keyandcableco/8bit8asterd/generate.py

#!/usr/bin/env python3
# 8-Bit 8asterd -- parameter bank generator.
#
# Copyright (C) 2026 Greg Miller, The Key & Cable Company
#
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
"""
8b8 parameter bank generator
============================

Single source of truth for the 8-Bit 8asterd's controllable parameters.
Edit PARAMS / PRESETS below, run this script, and it regenerates:

  parameters.h   -> include from the firmware (.ino). Param indices, ranges,
                    defaults, and a layout-version byte used to invalidate
                    stale EEPROM saves whenever the definition changes.
  index.html     -> the Web Serial control panel (Chrome/Edge, open the file
                    directly). All controls, groupings, display scaling and
                    factory presets are generated from PARAMS/PRESETS.

Protocol (USB-CDC serial, 115200, newline-terminated ASCII):
  P:<idx>:<value>   set one parameter        -> reply  V:<idx>:<clamped>
  DUMP              request all values       -> reply  PRESET:<v0>,<v1>,...
  LOAD:<v0>,<v1>,.. apply a full preset      -> reply  PRESET:...
  SAVE              persist params to EEPROM -> reply  SAVED:1
  DEFAULTS          restore factory defaults -> reply  PRESET:...

A preset is nothing more than the PRESET: CSV — an array of values in
parameter-index order, same idea as the minichord's parameter banks.
"""

import json
import os
import sys

from temperaments import PROFILES as TEMPER_PROFILES

# Panel labels per temperament, in profile order. Enum buttons are narrow, so
# a few are abbreviated; the full names stay in temperaments.py. Any profile
# without an entry here shows its own label, so a new one appears unnamed
# rather than not at all.
TEMPER_SHORT = {"quarter-comma meantone": "Meantone", "five-limit just (C major)": "Just",
                "pythagorean": "Pythag", "werckmeister III": "Werck III",
                "kirnberger III": "Kirn III", "vallotti": "Vallotti",
                "young no. 2": "Young", "kellner": "Kellner",
                "sixth-comma meantone": "1/6 Mean", "equal": "Equal"}
TEMPER_LABELS = [TEMPER_SHORT.get(p["name"], p["label"]) for p in TEMPER_PROFILES]

# ---------------------------------------------------------------------------
# Parameter definitions
# ---------------------------------------------------------------------------
# kind:    "toggle" (0/1 switch), "int" (slider), "enum" (button row; the
#          stored value is the option INDEX — firmware maps it to hardware
#          values where needed, e.g. buzz shape index -> AY shape register)
# scale/unit/offset: display only. shown = (value + offset) * scale
# help:    one line shown under the control
#
# All values must fit in a uint8_t (0..255) — the firmware stores the bank
# as a flat uint8_t array and EEPROM-persists it byte-for-byte.

PARAMS = [
    # --- Buzzy Bass --------------------------------------------------------
    dict(key="buzz_enable", label="Enable", group="Buzzy Bass", kind="toggle",
         default=0,
         help="Points the lowest held note's volume at the chip's envelope generator. Set to a looping shape it is an oscillator, so the note becomes a sawtooth or triangle rather than a square."),
    dict(key="buzz_ratio", label="Ratio", group="Buzzy Bass", kind="int",
         min=1, max=8, default=1,
         help="How far below the note the envelope oscillates: 1 is unison, 2 an octave down, 4 two octaves. At unison it is a waveform; lower it becomes a sub-oscillator."),
    dict(key="buzz_shape", label="Shape", group="Buzzy Bass", kind="enum",
         options=["Saw \u2193", "Tri \u2193\u2191", "Saw \u2191", "Tri \u2191\u2193"],
         default=0,
         help="Which looping envelope shape the hardware runs: 0 and 2 are sawtooths, 1 and 3 triangles. This is where a non-square waveform comes from -- the chip has no other."),
    dict(key="buzz_pure", label="Pure", group="Buzzy Bass", kind="toggle",
         default=0,
         help="Closes the channel's tone gate, so only the envelope reaches "
              "the output. Off, the square still gates the envelope and you "
              "hear the product of the two; on, you get the hardware "
              "sawtooth or triangle by itself."),
    dict(key="buzz_detune", label="Detune", group="Buzzy Bass", kind="int",
         min=0, max=64, default=32, offset=-32,
         help="Offsets the envelope against the square wave. Non-zero gives "
              "the sweeping 'MadMax buzzer' beat. 0 = locked together."),

    # --- Warp Zone (digital circuit bending) -------------------------------
    # Software versions of what a hardware bend does: hit the chip with
    # writes it was never meant to get, fast, while notes are sounding.
    # These write STRAIGHT to the chip, bypassing the register cache, so the
    # normal voice updates keep fighting them -- that fight is the sound.
    dict(key="warp_mode", label="Mode", group="Warp Zone", kind="enum",
         options=["Off", "Sync Buzz", "Stutter", "Scramble", "Zap",
                  "Tape Stop", "Siren", "Crush", "Ring", "Env Crush",
                  "SID Voice"],
         default=0,
         help="Sync Buzz restarts the envelope. Stutter gates the mixer. "
              "Scramble throws junk at registers. Zap sweeps noise. The "
              "last four move on their own: Tape Stop drags pitch down and "
              "snaps back, Siren sweeps it, Crush quantises it coarser and "
              "coarser, Ring is audio-rate amplitude modulation."),
    dict(key="warp_rate", label="Rate", group="Warp Zone", kind="int",
         min=1, max=120, default=30,
         help="Low = slow chopping. High reaches audio rate and becomes a "
              "tone in its own right. In Clock Warp, 1 holds the clock down "
              "instead of sweeping it, the way a clock-halving switch does."),
    dict(key="warp_depth", label="Depth", group="Warp Zone", kind="int",
         min=1, max=63, default=20,
         help="How violent the effect is."),
    dict(key="clock_enable", label="Enable", group="Clock Warp", kind="toggle",
         default=0,
         help="Wobbles the AY master clock, which the Leonardo generates, so "
              "it sits upstream of all three chips: pitch, noise colour, "
              "envelope rates and drum decays move together. It touches no "
              "chip register, so it runs alongside any Warp Zone mode."),
    dict(key="clock_drop", label="Drop", group="Clock Warp", kind="int",
         min=0, max=63, default=30,
         help="How far the clock falls. Around 45 matches the halving a "
              "YM2149 gives with its SEL pin low; full reaches 380kHz, below "
              "anything a hardware switch does."),
    dict(key="clock_sweep", label="Sweep", group="Clock Warp", kind="int",
         min=1, max=120, default=20,
         help="How fast the clock wanders. Only audible while Hold is below "
              "maximum, since a held clock does not sweep."),
    dict(key="clock_hold", label="Hold", group="Clock Warp", kind="int",
         min=0, max=63, default=0,
         help="Mixes between sweeping and sitting at the bottom of the "
              "sweep. Full is a clock-halving switch held down, which is "
              "where the coarse, slow character lives."),

    dict(key="warp_motion", label="Motion", group="Warp Zone", kind="int",
         min=0, max=64, default=0,
         help="Sweeps Rate up and down on its own, hands free. The sweep "
              "itself is usually the interesting part, not where it "
              "settles. 0 = Rate stays put."),

    # --- Vibrato -----------------------------------------------------------
    dict(key="wave_enable", label="Enable", group="Wavetable", kind="toggle",
         default=0,
         help="Takes over one channel and writes its volume register from a "
              "table at audio rate, tone off. The register becomes a 4-bit "
              "DAC, so the voice plays a real waveform instead of a square. "
              "Costs a voice and follows the highest note held."),
    dict(key="wave_shape", label="Shape", group="Wavetable", kind="enum",
         options=["Sine", "Triangle", "Saw", "Ramp", "Pulse 25%", "Vocal"],
         default=0,
         help="Sine and triangle are softer than anything the chip makes on "
              "its own. Pulse gives the narrow-square sound the AY cannot do "
              "in hardware. Vocal is a formant shape, somewhere near an 'ah'."),
    dict(key="wave_level", label="Level", group="Wavetable", kind="int",
         min=1, max=15, default=12,
         help="Peak of the waveform. Low values lose resolution fast, since "
              "there are only sixteen amplitude steps to draw it with."),

    dict(key="draw_enable", label="Enable", group="Drawbars", kind="toggle",
         default=0,
         help="Adds harmonics of each note on further voices, the way an "
              "organ's drawbars do. Summed squares at these ratios reshape "
              "the timbre rather than just thickening it, which is the only "
              "route to a new tone colour on a chip with no filter. Costs a "
              "voice per stop, so polyphony falls accordingly."),
    dict(key="draw_a", label="Stop 1", group="Drawbars", kind="enum",
         options=["Off", "16'", "5 1/3'", "4'", "2 2/3'", "2'", "1 3/5'", "1 1/3'", "1'"],
         default=3,
         help="Pitch of the first added stop, in organ footages against the "
              "note at 8'. 16' is an octave below, 4' an octave above, "
              "2 2/3' a twelfth above."),
    dict(key="draw_a_level", label="Level 1", group="Drawbars", kind="int",
         min=1, max=15, default=8,
         help="How loud the first stop sits under the note."),
    dict(key="draw_b", label="Stop 2", group="Drawbars", kind="enum",
         options=["Off", "16'", "5 1/3'", "4'", "2 2/3'", "2'", "1 3/5'", "1 1/3'", "1'"],
         default=0,
         help="Pitch of the second added stop. Off leaves the voice free for "
              "polyphony."),
    dict(key="draw_b_level", label="Level 2", group="Drawbars", kind="int",
         min=1, max=15, default=6,
         help="How loud the second stop sits under the note."),

    dict(key="uni_enable", label="Enable", group="Unison", kind="toggle",
         default=0,
         help="Doubles each melodic note on a second voice a little out of "
              "tune with the first. Halves how many notes can sound at once, "
              "and the beating between the pair is what makes it wide."),
    dict(key="uni_detune", label="Detune", group="Unison", kind="int",
         min=1, max=32, default=8,
         help="How far apart the pair sits. Low values beat slowly and "
              "thicken; high values drift towards a chorus or an out-of-tune "
              "honky-tonk."),

    dict(key="vib_enable", label="Enable", group="Vibrato", kind="toggle",
         default=0,
         help="Pitch LFO on all sounding melodic voices. Drums untouched."),
    dict(key="vib_rate", label="Rate", group="Vibrato", kind="int",
         min=1, max=200, default=50, scale=0.1, unit="Hz",
         help=""),
    dict(key="vib_depth", label="Depth", group="Vibrato", kind="int",
         min=0, max=31, default=6,
         help=""),
    dict(key="vib_delay", label="Delay", group="Vibrato", kind="int",
         min=0, max=200, default=0, scale=10, unit="ms",
         help="Onset delay after note start, then fades in."),

    # --- Tremolo -----------------------------------------------------------
    dict(key="trem_enable", label="Enable", group="Tremolo", kind="toggle",
         default=0,
         help="Volume LFO on melodic voices."),
    dict(key="trem_rate", label="Rate", group="Tremolo", kind="int",
         min=1, max=200, default=40, scale=0.1, unit="Hz",
         help=""),
    dict(key="trem_depth", label="Depth", group="Tremolo", kind="int",
         min=0, max=15, default=5,
         help="How many volume steps the LFO cuts (AY volume is 0\u201315)."),

    # --- Noise Blend -------------------------------------------------------
    dict(key="noise_enable", label="Enable", group="Noise Blend", kind="toggle",
         default=0,
         help="Mixes the AY noise generator into melodic voices."),
    dict(key="noise_period", label="Period", group="Noise Blend", kind="int",
         min=0, max=15, default=8,
         help="Higher = darker noise. Per-chip register, shared with drums."),

    # --- Drums (global shaping of the CH10 kit) ----------------------------
    # These scale the built-in kit table in the firmware rather than
    # replacing it, so one set of controls reshapes every drum at once and
    # still fits the flat preset array.
    dict(key="drum_tune", label="Tune", group="Drums", kind="int",
         min=50, max=200, default=100, unit="%",
         help="Pitch of every tuned drum. 100 = the kit as built."),
    dict(key="drum_decay", label="Decay", group="Drums", kind="int",
         min=50, max=200, default=100, unit="%",
         help="Length of every drum. Higher = longer tails."),
    dict(key="drum_bend", label="Bend", group="Drums", kind="int",
         min=0, max=200, default=100, unit="%",
         help="Pitch-drop amount on kicks and toms. 0 = flat, no sweep."),
    dict(key="drum_noise", label="Noise", group="Drums", kind="int",
         min=0, max=14, default=7, offset=-7,
         help="Noise colour. Negative = brighter/hissier, positive = darker."),

    # --- Drum FX -----------------------------------------------------------
    # Drums are the only voices driven by the AY envelope generator, so
    # these reach things the tone effects cannot: restarting the envelope
    # mid-hit, running it backwards, and varying it per strike.
    dict(key="drum_roll", label="Roll", group="Drum FX", kind="int",
         min=0, max=50, default=0, unit="Hz",
         help="Re-strikes the envelope while a drum is still ringing. Low "
              "values flam, high values become a buzz roll. The fader is "
              "spaced by ratio rather than by Hz, so it moves evenly by ear "
              "all the way up. 0 = off."),
    dict(key="drum_flam", label="Flam", group="Drum FX", kind="int",
         min=0, max=30, default=0, scale=10, unit="ms",
         help="Every hit fires a second time this long after. 0 = off."),
    dict(key="drum_reverse", label="Reverse", group="Drum FX", kind="toggle",
         default=0,
         help="Runs the envelope upward so drums swell instead of decay, "
              "then cut. Reverse-cymbal territory."),
    dict(key="drum_chaos", label="Chaos", group="Drum FX", kind="int",
         min=0, max=63, default=0,
         help="Randomises pitch, noise colour and length on every single "
              "hit, so no two strikes are identical."),

    # --- Auto FX (NES tracker style, automatic per note) -------------------
    # The 2A03's sweep unit did pitch slides in hardware; its chord and
    # retrigger sounds came from the tracker re-writing registers every
    # frame. Both are software here, applied automatically on every note.
    dict(key="arp_mode", label="Arp", group="Auto FX", kind="enum",
         options=["Off", "Maj", "Min", "Oct", "5th", "Dim", "Wide"],
         default=0,
         help="Cycles one voice through a chord fast enough to hear it as a "
              "chord. The classic chiptune fake-polyphony trick."),
    dict(key="arp_rate", label="Arp Rate", group="Auto FX", kind="int",
         min=1, max=50, default=17, unit="Hz",
         help="Steps per second. Around 15-25 is the classic NES rattle."),
    dict(key="sweep_amount", label="Sweep", group="Auto FX", kind="int",
         min=0, max=64, default=32, offset=-32,
         help="Automatic pitch slide on every note, like the NES sweep "
              "unit. Negative falls, positive rises, 0 is off."),
    dict(key="retrig_rate", label="Retrigger", group="Auto FX", kind="int",
         min=0, max=50, default=0, unit="Hz",
         help="Re-strikes the envelope while a note is held. Spaced by "
              "ratio rather than by Hz, so it moves evenly by ear. 0 = off."),

    # --- Envelope ----------------------------------------------------------
    dict(key="env_mode", label="Mode", group="Envelope", kind="enum",
         options=["MIDI ch presets", "Custom ADSR"], default=0,
         help="Presets = the original per-MIDI-channel tones[] table."),
    dict(key="env_attack", label="Attack", group="Envelope", kind="int",
         min=1, max=32, default=1,
         help="How long the note takes to reach full level, from 10ms at 1 up to 4s at 32. Spaced by ratio, so the fader moves evenly by ear."),
    dict(key="env_decay", label="Decay", group="Envelope", kind="int",
         min=1, max=32, default=26,
         help="How long it takes to fall from full level to the Sustain "
              "level. Spaced by ratio, so the fader moves evenly by ear."),
    dict(key="env_sustain", label="Sustain", group="Envelope", kind="int",
         min=0, max=32, default=32,
         help=""),
    dict(key="env_release", label="Release", group="Envelope", kind="int",
         min=1, max=32, default=19,
         help="How long the note takes to fade once you let go."),

    # --- Pitch & Response --------------------------------------------------
    dict(key="glide", label="Glide", group="Pitch & Response", kind="int",
         min=0, max=100, default=0,
         help="Portamento from the previous note. 0 = off, higher = slower."),
    dict(key="transpose", label="Transpose", group="Pitch & Response", kind="int",
         min=0, max=48, default=24, offset=-24, unit="st",
         help=""),
    # --- Master Mixer ------------------------------------------------------
    dict(key="mix_noise", label="Noise", group="Mixer", kind="int",
         min=0, max=15, default=15,
         help="Master noise level. The chip has no noise fader -- tone and "
              "noise share one amplitude -- so this gates the noise on and "
              "off a few thousand times a second with a random duty. Random "
              "rather than regular keeps the artefact broadband, so it reads "
              "as quieter noise instead of a whine. 15 = untouched."),
    dict(key="mix_tone", label="Tone", group="Mixer", kind="int",
         min=0, max=15, default=15,
         help="Master level for the pitched voices. Drums are unaffected."),
    dict(key="mix_drum", label="Drums", group="Mixer", kind="int",
         min=0, max=15, default=15,
         help="Master drum level. Below 15 this moves drums off the chip's "
              "hardware envelope onto a software one so the level can be "
              "scaled at all, which softens the transient slightly. "
              "15 leaves them on the hardware envelope, untouched."),

    dict(key="temperament", label="Temperament", group="Tuning", kind="enum",
         # Derived from temperaments.py rather than typed out, so a
         # temperament added there reaches the parameter's range. A hand copy
         # stopped at ten and the firmware clamped anything past it away.
         options=[TEMPER_LABELS[i] for i in range(len(TEMPER_LABELS))],
         default=0,
         help="Historical tunings, and two divisions of the octave. Audible in "
              "the lower octaves; above about MIDI 72 the AY's integer divisor "
              "is too coarse to render the offsets and they round away. 19-EDO "
              "and 31-EDO put twelve of their notes on the keys in the meantone "
              "layout; Root moves that layout with the key."),
    dict(key="temper_root", label="Root", group="Tuning", kind="enum",
         options=["C", "C#", "D", "D#", "E", "F", "F#", "G", "G#", "A", "A#", "B"],
         default=0,
         help="Which key the temperament is centred on. The root itself is "
              "exactly in tune; everything else is tempered around it."),

    dict(key="vel_sense", label="Velocity", group="Pitch & Response", kind="toggle",
         default=1,
         help="Off = every note plays at full volume."),
]

# Factory presets, defined by key so they survive reordering of PARAMS.
# Missing keys fall back to the parameter's default.
# Patches kept out of the normal list because they sit at the far end of
# several controls at once. Not unstable in the sense of crashing -- the
# clamps still hold -- but loud, detuned and hard to play.
HIDDEN_PRESETS = {
    "Dead Air":     dict(clock_enable=1, clock_drop=63, clock_hold=63,
                         warp_mode=7, warp_rate=90, warp_depth=55),
    "Wasp Factory": dict(warp_mode=10, warp_rate=120, warp_depth=63,
                         wave_enable=1, wave_shape=4, wave_level=15),
    "Cathedral":    dict(draw_enable=1, draw_a=1, draw_a_level=15,
                         draw_b=4, draw_b_level=12,
                         buzz_enable=1, buzz_pure=1, buzz_ratio=2),
    "Wrong Speed":  dict(clock_enable=1, clock_drop=50, clock_hold=20,
                         clock_sweep=3, uni_enable=1, uni_detune=26),
    "Hornet":       dict(warp_mode=10, warp_rate=120, warp_depth=63,
                         buzz_enable=1, buzz_ratio=1, buzz_detune=6,
                         draw_enable=1, draw_a=8, draw_a_level=9),
}

PRESETS = {
    "Init": {},
    "Buzz Bass Lead": dict(buzz_enable=1, buzz_ratio=1, buzz_shape=0,
                           vib_enable=1, vib_rate=55, vib_depth=5, vib_delay=60),
    "Haunted Organ": dict(vib_enable=1, vib_rate=30, vib_depth=12,
                          trem_enable=1, trem_rate=35, trem_depth=6,
                          env_mode=1, env_attack=22, env_decay=30,
                          env_sustain=28, env_release=21),
    "Wind Machine": dict(noise_enable=1, noise_period=13,
                         trem_enable=1, trem_rate=25, trem_depth=7,
                         env_mode=1, env_attack=20, env_decay=32,
                         env_sustain=30, env_release=30, vel_sense=0),
    "Chip Whistle": dict(transpose=36, glide=25,
                         vib_enable=1, vib_rate=80, vib_depth=4, vib_delay=40),
    "808 Kit": dict(drum_tune=78, drum_decay=165, drum_bend=130, drum_noise=9),
    "Tight Kit": dict(drum_tune=118, drum_decay=62, drum_bend=70, drum_noise=5),
    "MadMax Buzzer": dict(buzz_enable=1, buzz_ratio=1, buzz_shape=1,
                          buzz_detune=38, env_mode=1, env_attack=1,
                          env_decay=31, env_sustain=30, env_release=24),
    "Arcade Warp": dict(warp_mode=1, warp_rate=95, warp_depth=40,
                        buzz_enable=1, buzz_ratio=2, buzz_detune=36),
    "Broken Cabinet": dict(warp_mode=3, warp_rate=22, warp_depth=55,
                           noise_enable=1, noise_period=6),
    "Tape Eaten": dict(warp_mode=5, warp_rate=70, warp_depth=34,
                       warp_motion=12),
    "Air Raid": dict(warp_mode=6, warp_rate=60, warp_depth=44,
                     warp_motion=20),
    "Dying Console": dict(warp_mode=7, warp_rate=48, warp_depth=40,
                          warp_motion=9, noise_enable=1, noise_period=9),
    "Ring Zone": dict(warp_mode=8, warp_rate=105, warp_depth=30,
                      warp_motion=26, buzz_enable=1, buzz_ratio=1),
    "Buzz Roll": dict(drum_roll=45, drum_decay=70, drum_chaos=10),
    "Drunk Drummer": dict(drum_flam=7, drum_chaos=38, drum_tune=92,
                          drum_decay=120),
    "Reverse Kit": dict(drum_reverse=1, drum_decay=150, drum_bend=40),
    "Broken Machine": dict(drum_roll=50, drum_chaos=58, drum_noise=4,
                           drum_decay=55, drum_bend=170),
    "Bad Ground": dict(warp_mode=3, warp_rate=6, warp_depth=38,
                       warp_motion=35, noise_period=6),
    "1-Up Arp": dict(arp_mode=1, arp_rate=20, env_mode=1, env_attack=1,
                     env_decay=28, env_sustain=26, env_release=26),
    "Laser Jump": dict(sweep_amount=52, env_mode=1, env_attack=1,
                       env_decay=25, env_sustain=6, env_release=30),
    "Machine Gun": dict(retrig_rate=38, noise_enable=1, noise_period=4,
                        env_mode=1, env_attack=1, env_decay=23,
                        env_sustain=10, env_release=28),
}

# ---------------------------------------------------------------------------
# Panel sections
# ---------------------------------------------------------------------------
# Tones and drums are different voices sharing the same three chips, and the
# FX reach across both. The panel says so out loud rather than leaving it to
# be discovered: each band is labelled with what it touches, and the Warp
# Zone sits across the bottom spanning both because it hits them differently.

# Where the published site lives. The social preview needs ABSOLUTE urls --
# Reddit, Discord and the rest will not resolve a relative one.
SITE_URL = "https://keyandcableco.github.io/8bit8asterd"
SITE_HOME = "https://keyandcable.com"
SITE_TITLE = "The 8Bit 8asterd"
SITE_DESC = ("A 9-voice chiptune synth built on three AY-3-8910 chips. "
             "Playable in your browser, running the same firmware as the hardware.")

SECTIONS = [
    dict(key="mix", title="Master Mixer", scope="everything out",
         blurb="Output levels. Tone and noise share one amplitude register "
               "per channel on this chip, so noise is thinned by gating "
               "rather than by a level control that does not exist.",
         groups=["Mixer"]),
    dict(key="tone", title="Tone Voices", scope="pitched voices",
         blurb="The melodic side. Nothing here touches the drum channel.",
         groups=["Envelope", "Tuning", "Pitch & Response", "Buzzy Bass", "Unison", "Drawbars", "Wavetable",
                 "Vibrato", "Tremolo", "Noise Blend", "Auto FX"]),
    dict(key="drum", title="Drum Voices", scope="MIDI channel 10",
         blurb="Percussion only. Drums are the voices driven by each chip's "
               "envelope generator, which is why the FX bite them hardest.",
         groups=["Drums", "Drum FX"]),
    dict(key="warp", title="Warp Zone", scope="tones + drums",
         blurb="The bent stuff, and the only section that reaches both. It "
               "writes straight to the chips while the voices keep writing "
               "their own values, so the two fight \u2014 and because drums "
               "run on the envelope generator and tones do not, the same "
               "setting lands very differently on each.",
         groups=["Warp Zone", "Clock Warp"]),
]

# ---------------------------------------------------------------------------
# Normalise + validate
# ---------------------------------------------------------------------------

def normalise():
    for i, p in enumerate(PARAMS):
        p["index"] = i
        if p["kind"] == "toggle":
            p.setdefault("min", 0); p.setdefault("max", 1)
        elif p["kind"] == "enum":
            p.setdefault("min", 0); p["max"] = len(p["options"]) - 1
        p.setdefault("scale", 1); p.setdefault("offset", 0)
        p.setdefault("unit", ""); p.setdefault("help", "")

        for field in ("min", "max", "default"):
            v = p[field]
            if not (0 <= v <= 255):
                sys.exit(f"ERROR: {p['key']}.{field}={v} does not fit uint8_t")
        if not (p["min"] <= p["default"] <= p["max"]):
            sys.exit(f"ERROR: {p['key']} default outside range")

    placed = {g for sec in SECTIONS for g in sec["groups"]}
    actual = {p["group"] for p in PARAMS}
    missing = actual - placed
    extra = placed - actual
    if missing:
        sys.exit(f"ERROR: parameter groups with no panel section: {sorted(missing)}")
    if extra:
        sys.exit(f"ERROR: SECTIONS lists groups that do not exist: {sorted(extra)}")

    keys = [p["key"] for p in PARAMS]
    if len(set(keys)) != len(keys):
        sys.exit("ERROR: duplicate parameter keys")

    for name, values in PRESETS.items():
        for k, v in values.items():
            match = [p for p in PARAMS if p["key"] == k]
            if not match:
                sys.exit(f"ERROR: preset '{name}' references unknown key '{k}'")
            p = match[0]
            if not (p["min"] <= v <= p["max"]):
                sys.exit(f"ERROR: preset '{name}' value {k}={v} outside range")


def preset_array(values):
    return [values.get(p["key"], p["default"]) for p in PARAMS]


def layout_version():
    """One byte derived from the definition, so firmware EEPROM saves are
    invalidated automatically whenever ranges/order/count change."""
    acc = len(PARAMS)
    for p in PARAMS:
        for ch in p["key"]:
            acc = (acc * 31 + ord(ch)) & 0xFF
        acc = (acc * 31 + p["min"] + p["max"] * 3 + p["default"] * 7) & 0xFF
    return acc or 1


# ---------------------------------------------------------------------------
# parameters.h
# ---------------------------------------------------------------------------

def emit_header(path):
    ver = layout_version()
    lines = []
    a = lines.append
    a("// AUTO-GENERATED by generate.py -- do not edit by hand.")
    a("// Edit PARAMS in generate.py and re-run it instead.")
    a("#ifndef PARAMETERS_H")
    a("#define PARAMETERS_H")
    a("")
    a("#include <avr/pgmspace.h>")
    a("")
    a(f"#define NUM_PARAMS {len(PARAMS)}")
    a(f"#define PARAM_LAYOUT_VERSION 0x{ver:02X}")
    a("")
    a("enum {")
    for p in PARAMS:
        a(f"  P_{p['key'].upper()} = {p['index']},  // {p['group']}: {p['label']}"
          f" [{p['min']}..{p['max']}] default {p['default']}")
    a("};")
    a("")
    for name, field in (("PARAM_MIN", "min"), ("PARAM_MAX", "max"),
                        ("PARAM_DEFAULT", "default")):
        vals = ", ".join(str(p[field]) for p in PARAMS)
        a(f"static const uint8_t {name}[NUM_PARAMS] PROGMEM = {{ {vals} }};")
    a("")
    a("// Ticks between events for the re-strike controls (Drum Roll,")
    a("// Retrigger), indexed by the parameter value. The tick is 100Hz, so")
    a("// ticks = 100 / rate. Rate is spaced EXPONENTIALLY rather than")
    a("// linearly: rhythm is heard in ratios, so a linear Hz control puts a")
    a("// doubling between the first two positions and nothing at all across")
    a("// the top half. This curve runs 1.5Hz to 45Hz at about 6% per step.")
    a("static const uint8_t RATE_EVERY[51] PROGMEM = {")
    import math
    LO, HI, N = 1.5, 45.0, 50
    vals = ["0"]
    for v in range(1, N + 1):
        rate = LO * (HI / LO) ** ((v - 1) / (N - 1))
        vals.append(str(max(1, min(255, round(100.0 / rate)))))
    for i in range(0, len(vals), 17):
        a("  " + ", ".join(vals[i:i + 17]) + ",")
    a("};")
    a("")
    a("// Tone-period multiplier for the Warp pitch modes, x256, indexed by")
    a("// warp depth. Pitch is heard in semitones, so the table is")
    a("// exponential: a linear multiplier put half the total drop in the")
    a("// first quarter of the fader. This spreads 30 semitones evenly.")
    a("static const uint16_t WARP_STRETCH[64] PROGMEM = {")
    import math
    sv = [str(int(round(256 * (2 ** (d * 30.0 / 63.0 / 12.0))))) for d in range(64)]
    for i in range(0, len(sv), 12):
        a("  " + ", ".join(sv[i:i + 12]) + ",")
    a("};")
    a("")
    a("// Envelope segment rates, in 1/16ths of an amplitude unit per 100Hz")
    a("// tick, indexed by the parameter value. The parameter is a TIME and")
    a("// the scale is exponential, 10ms to 4s: as a linear per-tick rate it")
    a("// was reciprocal, so 1->2 halved the time while 31->32 moved it 4ms.")
    a("// A 1/16th accumulator keeps the slow end usable, which an integer")
    a("// rate could not -- 1023/400 rounds to 3 and swallows the top third")
    a("// of the fader.")
    a("static const uint16_t ENV_RATE[33] PROGMEM = {")
    ev = ["0"]
    for v in range(1, 33):
        t = 1.0 * (400.0 ** ((v - 1) / 31.0))
        ev.append(str(max(1, min(65535, int(round(1023.0 * 16.0 / t))))))
    for i in range(0, len(ev), 11):
        a("  " + ", ".join(ev[i:i + 11]) + ",")
    a("};")
    a("")
    a("// Master mixer attenuation, in amplitude-register steps, indexed by")
    a("// the mixer setting. Applied by SUBTRACTION, which is a true dB cut")
    a("// and treats a quiet note the same as a loud one -- multiplying the")
    a("// register instead truncated a decaying note to silence several fader")
    a("// positions before a full one. The curve is an audio taper: the top")
    a("// half covers about 13dB and it accelerates below that, because the")
    a("// AY's own steps grow from roughly 1.5dB at the top to 3.5dB at the")
    a("// bottom and a straight mapping therefore dives.")
    a("static const uint8_t MIX_ATTEN[16] PROGMEM = {")
    a("  15, 13, 11, 10, 9, 8, 7, 6, 5, 4, 3, 2, 2, 1, 1, 0")
    a("};")
    a("")
    a("// Wavetable voice. Sixty-four steps, values 0..15 -- the amplitude")
    a("// register IS the output once tone and noise are switched off, so")
    a("// this is a 4-bit DAC and these are the waveforms it draws. Four bits")
    a("// is coarse, which is the point: it sounds like the hardware it is.")
    a("#define WAVE_LEN 64")
    a("#define WAVE_COUNT 6")
    a("static const uint8_t WAVE_TABLES[WAVE_COUNT][WAVE_LEN] PROGMEM = {")
    import math
    def emit(name, fn):
        vals = []
        for i in range(64):
            v = fn(i / 64.0)
            vals.append(str(max(0, min(15, int(round(v * 15))))))
        a("  { // " + name)
        for j in range(0, 64, 16):
            a("    " + ", ".join(vals[j:j + 16]) + ",")
        a("  },")
    emit("sine",      lambda t: 0.5 + 0.5 * math.sin(2 * math.pi * t))
    emit("triangle",  lambda t: 2 * t if t < 0.5 else 2 * (1 - t))
    emit("saw down",  lambda t: 1 - t)
    emit("ramp up",   lambda t: t)
    emit("pulse 25%", lambda t: 1.0 if t < 0.25 else 0.0)
    # Two stacked formants, roughly an "ah": the chip cannot filter, so the
    # shape has to carry the resonance itself.
    emit("vocal", lambda t: 0.5 + 0.30 * math.sin(2 * math.pi * t)
                                + 0.22 * math.sin(2 * math.pi * 3 * t + 0.4)
                                + 0.12 * math.sin(2 * math.pi * 5 * t + 1.1))
    a("};")
    a("")
    a("#endif // PARAMETERS_H")
    with open(path, "w") as f:
        f.write("\n".join(lines) + "\n")
    print(f"wrote {path}  ({len(PARAMS)} params, layout version 0x{ver:02X})")


# ---------------------------------------------------------------------------
# index.html
# ---------------------------------------------------------------------------

HTML_TEMPLATE = r"""<!doctype html>
<html lang="en">
<head>
<meta charset="utf-8" />
<meta name="viewport" content="width=device-width, initial-scale=1" />
<title>8B8 — AY Panel</title>
<meta name="description" content="__SITE_DESC__">

<!-- Open Graph. Reddit, Discord, iMessage and Slack all read these; without
     them a shared link renders as a bare url with no picture. -->
<meta property="og:type" content="website">
<meta property="og:site_name" content="The Key &amp; Cable Company">
<meta property="og:title" content="__SITE_TITLE__">
<meta property="og:description" content="__SITE_DESC__">
<meta property="og:url" content="__SITE_URL__/">
<meta property="og:image" content="__SITE_URL__/social.png">
<meta property="og:image:width" content="1200">
<meta property="og:image:height" content="630">
<meta property="og:image:alt" content="The 8Bit 8asterd control panel">
<meta name="twitter:card" content="summary_large_image">
<meta name="twitter:title" content="__SITE_TITLE__">
<meta name="twitter:description" content="__SITE_DESC__">
<meta name="twitter:image" content="__SITE_URL__/social.png">

<link rel="preconnect" href="https://fonts.googleapis.com">
<link href="https://fonts.googleapis.com/css2?family=Press+Start+2P&family=JetBrains+Mono:wght@400;500;700&display=swap" rel="stylesheet">
<style>
  /* ---- Themes --------------------------------------------------------
     Three cabinets, one layout. Every colour is a variable so a theme is
     just a different set of them; --ui-scale multiplies every type size so
     the whole panel can be sized without reflowing anything. ---------- */

  :root{
    --ui-scale: 1;
    --pixel:'Press Start 2P', monospace;
    --mono:'JetBrains Mono', ui-monospace, monospace;
    --glow: none;
    --body-bg: var(--slot);
  }

  /* NES front-loader: two greys over a near-black slot, red as the only colour */
  :root, [data-theme="nes"]{
    --slot:#0b0b0c; --body-dark:#2e2f31; --body:#3c3d40; --body-lit:#5a5c60;
    --bezel:#17181a; --accent:#c8322b; --accent-lit:#e8483f; --accent-dim:#6d1f1b;
    --text:#dedbd2; --text-dim:#8c8d90; --ok:#7bbf5a; --warn:#d8c98a;
    --on-accent:#ffffff;
    --body-bg:
      repeating-linear-gradient(0deg, rgba(255,255,255,.012) 0 2px, transparent 2px 4px),
      #0b0b0c;
  }

  /* Arcade cabinet: black glass, CRT scanlines, neon on the marquee */
  [data-theme="arcade"]{
    --slot:#05060a; --body-dark:#0d1030; --body:#151a44; --body-lit:#2b3480;
    --bezel:#000208; --accent:#ff2e88; --accent-lit:#ff6ab0; --accent-dim:#6b0f38;
    --text:#e8f4ff; --text-dim:#7f93c4; --ok:#3dffc0; --warn:#ffd400;
    --on-accent:#0a0010;
    --glow: 0 0 6px currentColor;
    --body-bg:
      repeating-linear-gradient(0deg, rgba(0,0,0,.55) 0 1px, transparent 1px 3px),
      radial-gradient(ellipse at 50% 0%, #1b2160 0%, #05060a 62%),
      #05060a;
  }

  /* Handheld: four shades of green and nothing else */
  [data-theme="handheld"]{
    --slot:#0b1a06; --body-dark:#1d3312; --body:#2b4a1a; --body-lit:#456b2a;
    --bezel:#050d03; --accent:#9bbc0f; --accent-lit:#c6de8c; --accent-dim:#4a5c11;
    --text:#c6de8c; --text-dim:#6b8a3a; --ok:#9bbc0f; --warn:#c6de8c;
    --on-accent:#0b1a06;
    --body-bg:
      repeating-linear-gradient(0deg, rgba(0,0,0,.10) 0 2px, transparent 2px 4px),
      #0b1a06;
  }

  *{ box-sizing:border-box; }
  html,body{ margin:0; padding:0; }
  body{
    background: var(--body-bg);
    color:var(--text); font-family:var(--mono);
    min-height:100vh; padding:26px 14px 56px;
    display:flex; justify-content:center;
  }
  .rack{ width:100%; max-width:1080px; }

  /* ---- Header ---- */
  header{
    background:linear-gradient(180deg, var(--body) 0%, var(--body-dark) 100%);
    border:2px solid var(--bezel);
    box-shadow: inset 0 2px 0 var(--body-lit), inset 0 -2px 0 rgba(0,0,0,.55);
    padding:0; margin-bottom:14px; overflow:hidden;
  }
  .stripe{ display:flex; height:9px; }
  .stripe i{ flex:1; background:var(--accent); }
  .stripe i:nth-child(even){ background:var(--body-dark); flex:0 0 26px; }
  [data-theme="arcade"] .stripe i{ background:var(--accent); }
  [data-theme="arcade"] .stripe i:nth-child(2){ background:#00e5ff; flex:1; }
  [data-theme="arcade"] .stripe i:nth-child(4){ background:var(--warn); flex:1; }

  .head-inner{
    display:flex; align-items:flex-end; justify-content:space-between;
    gap:16px; flex-wrap:wrap; padding:16px 18px 18px;
  }
  .brand .eyebrow{
    display:flex; align-items:center; gap:9px;
    font-family:var(--pixel); font-size:calc(7px * var(--ui-scale));
    letter-spacing:.12em; color:var(--text-dim); margin-bottom:9px;
  }
  .brand .eyebrow .brandlink{
    display:flex; align-items:center; gap:9px;
    color:inherit; text-decoration:none; cursor:pointer;
  }
  .brand .eyebrow .brandlink:hover{ color:var(--accent-lit); }
  .brand .eyebrow .brandlink:hover img{ filter:brightness(1.15); }
  .brand .eyebrow img{
    height:calc(20px * var(--ui-scale)); width:auto; display:block;
    image-rendering:auto;
  }
  .brand h1{
    font-family:var(--pixel); font-size:calc(19px * var(--ui-scale));
    margin:0; line-height:1.35; color:var(--text);
    text-shadow:2px 2px 0 rgba(0,0,0,.65);
  }
  .brand h1 span{ color:var(--accent-lit); text-shadow:var(--glow); }
  .brand p{
    margin:10px 0 0; color:var(--text-dim);
    font-size:calc(12px * var(--ui-scale)); max-width:52ch; line-height:1.55;
  }

  .connection{ display:flex; align-items:center; gap:9px; flex-wrap:wrap; }
  .status-pill{
    display:flex; align-items:center; gap:7px; font-family:var(--pixel);
    font-size:calc(7px * var(--ui-scale)); letter-spacing:.06em;
    padding:9px 11px; background:var(--slot);
    border:2px solid var(--bezel); color:var(--text-dim);
  }
  .status-pill .dot{ width:7px; height:7px; background:var(--text-dim); }
  .status-pill.on{ color:var(--ok); }
  .status-pill.on .dot{ background:var(--ok); box-shadow:0 0 7px var(--ok); }
  .status-pill.err{ color:var(--accent-lit); }
  .status-pill.err .dot{ background:var(--accent-lit); box-shadow:0 0 7px var(--accent); }

  button.btn{
    font-family:var(--pixel); font-size:calc(7px * var(--ui-scale));
    letter-spacing:.04em; color:var(--text); cursor:pointer; padding:10px 12px;
    background:linear-gradient(180deg, var(--body) 0%, var(--body-dark) 100%);
    border:2px solid var(--bezel);
    box-shadow: inset 0 2px 0 var(--body-lit), inset 0 -2px 0 rgba(0,0,0,.5);
  }
  button.btn:hover{ color:var(--accent-lit); text-shadow:var(--glow); }
  button.btn:active{ box-shadow: inset 0 2px 4px rgba(0,0,0,.7); transform:translateY(1px); }
  button.btn:disabled{ opacity:.35; cursor:not-allowed; }
  button.btn:focus-visible, .switch:focus-visible, .enum-btn:focus-visible{
    outline:2px solid var(--accent-lit); outline-offset:2px;
  }

  select{
    font-family:var(--mono); font-size:calc(12px * var(--ui-scale));
    font-weight:500; background:var(--slot); color:var(--text);
    border:2px solid var(--bezel); padding:9px;
  }

  .unsupported, .mismatch{
    background:var(--body-dark); border:2px solid var(--accent);
    padding:14px 16px; color:var(--text);
    font-size:calc(12px * var(--ui-scale)); line-height:1.6; margin-bottom:16px;
  }
  .unsupported b, .mismatch b{
    color:var(--accent-lit); font-family:var(--pixel);
    font-size:calc(8px * var(--ui-scale)); display:block;
    margin-bottom:7px; line-height:1.5;
  }
  .mismatch code{ background:var(--slot); padding:1px 5px; color:var(--text); }

  /* ---- Control bars ---- */
  .bar{
    display:flex; align-items:center; gap:8px; flex-wrap:wrap;
    background:linear-gradient(180deg, var(--body) 0%, var(--body-dark) 100%);
    border:2px solid var(--bezel);
    box-shadow: inset 0 2px 0 var(--body-lit), inset 0 -2px 0 rgba(0,0,0,.55);
    padding:12px 13px; margin-bottom:12px;
  }
  .bar .label{
    font-family:var(--pixel); font-size:calc(7px * var(--ui-scale));
    color:var(--text-dim); margin-right:4px;
  }
  .bar .spacer, .transport .spacer{ flex:1 1 auto; }
  .bar.settings{ border-top-width:0; }
  /* .bar sets display:flex, and a class rule beats the browser's default
     [hidden]{display:none} -- so the panel needs this or it never hides. */
  .bar[hidden]{ display:none; }

  /* Compact: drop the explanatory text once you know what things do. */
  body.compact .ctl .help{ display:none; }
  body.compact .section-blurb{ display:none; }
  body.compact .ctl{ margin-bottom:10px; }


  /* ---- Labelled control cells: label under the control it belongs to,
         because a row of labels beside a row of controls is ambiguous ---- */
  .cc-row{
    display:flex; gap:14px; flex-wrap:wrap; align-items:flex-end;
    padding:12px 13px;
  }
  .cc{ display:flex; flex-direction:column; align-items:center; gap:6px; }
  .cc > .cc-label{
    font-family:var(--pixel); font-size:calc(6px * var(--ui-scale));
    color:var(--text-dim); letter-spacing:.04em; text-align:center;
    white-space:nowrap;
  }
  .cc select{ padding:7px 8px; font-size:calc(11px * var(--ui-scale)); }
  .cc .readout{
    font-family:var(--pixel); font-size:calc(10px * var(--ui-scale));
    color:var(--accent-lit); background:var(--slot);
    border:2px solid var(--bezel); padding:9px 14px; min-width:88px;
    text-align:center;
  }

  /* ---- Custom scale degrees ---- */
  .degrees{ display:flex; gap:4px; flex-wrap:wrap; padding:0 13px 12px; }
  .degrees .deg{
    font-family:var(--pixel); font-size:calc(6px * var(--ui-scale));
    padding:9px 0; width:38px; text-align:center; cursor:pointer;
    background:var(--slot); border:2px solid var(--bezel); color:var(--text-dim);
    user-select:none;
  }
  .degrees .deg.on{ background:var(--accent); color:var(--on-accent); }
  .degrees .note{
    font-family:var(--mono); font-size:calc(10px * var(--ui-scale));
    color:var(--text-dim); align-self:center; margin-left:6px;
  }

  /* ---- Octave steppers ---- */
  .oct{ display:flex; align-items:center; gap:0; flex:none; }
  .oct button{
    font-family:var(--pixel); font-size:calc(9px * var(--ui-scale));
    width:30px; height:30px; cursor:pointer; color:var(--text);
    background:linear-gradient(180deg, var(--body) 0%, var(--body-dark) 100%);
    border:2px solid var(--bezel);
  }
  .oct button:hover{ color:var(--accent-lit); }
  .oct button:active{ background:var(--accent); color:var(--on-accent); }
  .oct span{
    min-width:34px; text-align:center; font-family:var(--pixel);
    font-size:calc(7px * var(--ui-scale)); color:var(--accent-lit);
    background:var(--slot); border:2px solid var(--bezel);
    border-left:0; border-right:0; padding:8px 0;
  }

  /* ---- Play surface: chord matrix, strumpad, keyboard ---- */
  .play-wrap{ display:flex; gap:14px; flex-wrap:wrap; padding:12px 13px; }
  .matrix{ flex:1 1 420px; }
  .matrix .cols{ display:grid; grid-template-columns:repeat(7,1fr); gap:4px; }
  .matrix .colhead{
    font-family:var(--pixel); font-size:calc(8px * var(--ui-scale));
    text-align:center; color:var(--text-dim); padding:5px 0 7px;
  }
  .chordbtn{
    font-family:var(--pixel); font-size:calc(7px * var(--ui-scale));
    padding:14px 2px; text-align:center; cursor:pointer; user-select:none;
    background:linear-gradient(180deg, var(--body-lit) 0%, var(--body) 100%);
    border:2px solid var(--bezel); color:var(--text); touch-action:none;
  }
  .chordbtn.row1{ background:linear-gradient(180deg, var(--body) 0%, var(--body-dark) 100%); }
  .chordbtn.row2{ background:linear-gradient(180deg, var(--body-dark) 0%, var(--slot) 100%); color:var(--text-dim); }
  .chordbtn.down, .chordbtn.latched{ background:var(--accent); color:var(--on-accent); }

  .strum{
    flex:0 0 120px; display:flex; flex-direction:column; gap:1px;
    touch-action:none; min-height:clamp(340px, 46vh, 560px);
  }
  .strum .seg{
    flex:1; border:1px solid var(--bezel); cursor:pointer;
    background:linear-gradient(90deg, var(--body-dark) 0%, var(--slot) 100%);
    display:flex; align-items:center; justify-content:center;
    font-family:var(--pixel); font-size:calc(5px * var(--ui-scale));
    color:var(--text-dim); line-height:1; overflow:hidden;
    pointer-events:auto;
  }
  .strum .seg > span{ pointer-events:none; }
  .strum .seg.lit, .strum .seg.held{ color:var(--on-accent); }
  /* Laid flat, the harp runs the full width under the matrix instead of
     standing beside it, which suits a phone held upright. */
  .strum.horiz{
    flex:1 1 100%; flex-direction:row; min-height:0; height:92px;
  }
  .strum.horiz .seg{
    background:linear-gradient(180deg, var(--body-dark) 0%, var(--slot) 100%);
    font-size:calc(6px * var(--ui-scale));
  }
  .strum.horiz .label{ display:none; }
  /* Grid: three across, like the minichord keymaster, which is far easier to
     hit accurately on a phone than a thin strip. */
  .strum.grid{
    flex:1 1 100%; display:grid; grid-template-columns:repeat(3,1fr);
    gap:3px; min-height:0; height:auto;
  }
  .strum.grid .seg{
    min-height:42px; border:2px solid var(--bezel);
    font-size:calc(7px * var(--ui-scale));
  }
  .strum.grid .label{ display:none; }
  .strum .seg.lit{ background:var(--accent); }
  .strum .seg.held{ background:var(--accent-lit); }
  .strum .label{
    font-family:var(--pixel); font-size:calc(7px * var(--ui-scale));
    color:var(--text-dim); text-align:center; padding-bottom:4px;
  }

  /* ---- Piano: whites in a row, blacks floated over the gaps ---- */
  .piano-scroll{ overflow-x:auto; padding:0 13px 10px; }
  .piano{
    position:relative; display:flex; gap:0;
    min-width:min(100%, 520px); height:clamp(90px, 18vw, 130px);
    touch-action:none; user-select:none;
  }
  .wkey{
    flex:1 0 0; min-width:26px; position:relative;
    background:linear-gradient(180deg, #e8e5dc 0%, #bdbab1 100%);
    border:2px solid var(--bezel); border-right-width:1px;
    border-radius:0 0 3px 3px; cursor:pointer;
  }
  .wkey:last-child{ border-right-width:2px; }
  .wkey.down{ background:linear-gradient(180deg, var(--accent-lit) 0%, var(--accent) 100%); }
  .wkey b{
    position:absolute; bottom:5px; left:0; right:0; text-align:center;
    font-family:var(--pixel); font-size:calc(6px * var(--ui-scale));
    color:#3a3a3a; pointer-events:none;
  }
  .bkey{
    position:absolute; top:0; height:62%; z-index:2;
    background:linear-gradient(180deg, #3a3a3d 0%, #121214 100%);
    border:2px solid var(--bezel); border-radius:0 0 3px 3px;
    cursor:pointer; transform:translateX(-50%);
  }
  .bkey.down{ background:linear-gradient(180deg, var(--accent) 0%, var(--accent-dim) 100%); }
  .bkey b{
    position:absolute; bottom:4px; left:0; right:0; text-align:center;
    font-family:var(--pixel); font-size:calc(6px * var(--ui-scale));
    color:#cfcfcf; pointer-events:none;
  }

  /* ---- Drum pads: big touch targets, nothing fiddly ---- */
  .pads{
    display:grid; grid-template-columns:repeat(auto-fit,minmax(78px,1fr));
    gap:6px; padding:0 13px 13px;
  }
  .pad{
    font-family:var(--pixel); font-size:calc(7px * var(--ui-scale));
    padding:18px 4px; text-align:center; cursor:pointer; user-select:none;
    background:linear-gradient(180deg, var(--accent-dim) 0%, var(--slot) 100%);
    border:2px solid var(--bezel); color:var(--text); touch-action:none;
  }
  .pad.down{ background:var(--accent); color:var(--on-accent); }
  .pad b{ display:block; font-size:calc(6px * var(--ui-scale)); opacity:.6; margin-bottom:5px; }

  /* ---- Transport: pinned so the sequencer can be stopped from any
         section, not only from the one it lives in ---- */
  .transport{
    position:sticky; top:env(safe-area-inset-top, 0px); z-index:50;
    display:flex; align-items:center; gap:12px;
    background:linear-gradient(180deg, var(--body) 0%, var(--body-dark) 100%);
    border:2px solid var(--bezel);
    box-shadow: inset 0 2px 0 var(--body-lit), 0 4px 10px rgba(0,0,0,.5);
    padding:10px 13px; margin-bottom:12px;
  }
  .transport .btn.play{
    font-size:calc(11px * var(--ui-scale));
    padding:13px 28px; min-width:110px;
    background:linear-gradient(180deg, var(--accent-lit) 0%, var(--accent) 100%);
    color:var(--on-accent);
  }
  .transport .btn.play.running{
    background:linear-gradient(180deg, var(--warn) 0%, var(--accent-dim) 100%);
  }
  .transport .tinfo{
    font-family:var(--pixel); font-size:calc(7px * var(--ui-scale));
    color:var(--text-dim); letter-spacing:.05em;
  }

  /* ---- File picker: a bare input[type=file] renders in OS colours, which
         on this panel is dark text on a dark background and looks like
         nothing is there at all ---- */
  .filepick{ display:flex; align-items:center; gap:10px; flex-wrap:wrap; }
  .filepick input[type=file]{ display:none; }
  .filepick label{
    font-family:var(--pixel); font-size:calc(7px * var(--ui-scale));
    padding:11px 16px; cursor:pointer; color:var(--text);
    background:linear-gradient(180deg, var(--body-lit) 0%, var(--body) 100%);
    border:2px solid var(--bezel);
  }
  .filepick label:hover{ color:var(--accent-lit); }
  .filepick .fname{
    font-family:var(--mono); font-size:calc(11px * var(--ui-scale));
    color:var(--text-dim);
  }

  /* ---- Sequencer ---- */
  /* Outside the pattern: clearly inactive, but a note placed there must
     still be legible -- at a quarter opacity it vanished entirely. */
  .step.past{ opacity:.55; border-style:dotted; }
  .step.past.on, .step.past.tail{ opacity:.7; }
  .seqrow.sharprow .seqname{ opacity:.6; }
  .step.note.on{ background:var(--warn); }

  /* ---- Transport: pinned so the sequencer can be stopped from any
         section, not only from the one it lives in ---- */
  .transport{
    position:sticky; top:env(safe-area-inset-top, 0px); z-index:50;
    display:flex; align-items:center; gap:12px;
    background:linear-gradient(180deg, var(--body) 0%, var(--body-dark) 100%);
    border:2px solid var(--bezel);
    box-shadow: inset 0 2px 0 var(--body-lit), 0 4px 10px rgba(0,0,0,.5);
    padding:10px 13px; margin-bottom:12px;
  }
  .transport .btn.play{
    font-size:calc(11px * var(--ui-scale));
    padding:13px 28px; min-width:110px;
    background:linear-gradient(180deg, var(--accent-lit) 0%, var(--accent) 100%);
    color:var(--on-accent);
  }
  .transport .btn.play.running{
    background:linear-gradient(180deg, var(--warn) 0%, var(--accent-dim) 100%);
  }
  .transport .tinfo{
    font-family:var(--pixel); font-size:calc(7px * var(--ui-scale));
    color:var(--text-dim); letter-spacing:.05em;
  }

  /* ---- File picker: a bare input[type=file] renders in OS colours, which
         on this panel is dark text on a dark background and looks like
         nothing is there at all ---- */
  .filepick{ display:flex; align-items:center; gap:10px; flex-wrap:wrap; }
  .filepick input[type=file]{ display:none; }
  .filepick label{
    font-family:var(--pixel); font-size:calc(7px * var(--ui-scale));
    padding:11px 16px; cursor:pointer; color:var(--text);
    background:linear-gradient(180deg, var(--body-lit) 0%, var(--body) 100%);
    border:2px solid var(--bezel);
  }
  .filepick label:hover{ color:var(--accent-lit); }
  .filepick .fname{
    font-family:var(--mono); font-size:calc(11px * var(--ui-scale));
    color:var(--text-dim);
  }

  /* ---- Sequencer ---- */
  .seq{ padding:0 13px 13px; overflow-x:auto; }
  .seqrow{ display:flex; align-items:center; gap:3px; margin-bottom:3px; }
  .seqname select{
    width:100%; font-size:calc(9px * var(--ui-scale)); padding:2px 1px;
  }
  .seqname{
    flex:0 0 86px; font-family:var(--pixel);
    font-size:calc(6px * var(--ui-scale)); color:var(--text-dim);
    cursor:pointer; padding:4px 0;
  }
  .seqname:hover{ color:var(--accent-lit); }
  .step{
    flex:1 1 0; min-width:18px; height:26px; cursor:pointer;
    background:var(--slot); border:2px solid var(--bezel); touch-action:none;
  }
  .step.beat{ border-color:var(--body-lit); }
  .step.on{ background:var(--accent); }
  .step.tail{ background:var(--accent-dim); }
  .step.note.tail{ background:var(--warn); opacity:.55; }
  .step.playing{ box-shadow:inset 0 0 0 2px var(--warn); }
  .seqhead{ display:flex; gap:3px; margin:0 0 5px 75px; }
  .seqhead div{
    flex:1 1 0; min-width:18px; text-align:center;
    font-family:var(--pixel); font-size:calc(6px * var(--ui-scale));
    color:var(--text-dim);
  }
  .seqhead div.beat{ color:var(--accent-lit); }

  /* ---- Gamepad ---- */
  .gp-grid{ display:grid; grid-template-columns:repeat(auto-fit,minmax(200px,1fr)); gap:10px; padding:0 13px 13px; }
  .gp-assign{ display:flex; align-items:center; gap:8px; }
  .gp-assign span{
    font-family:var(--pixel); font-size:calc(6px * var(--ui-scale));
    color:var(--text-dim); flex:0 0 68px;
  }
  .gp-assign select{ flex:1 1 auto; min-width:0; }
  .gp-live{
    font-family:var(--mono); font-size:calc(11px * var(--ui-scale));
    color:var(--text-dim); padding:0 13px 12px; line-height:1.7;
  }
  .gp-live b{ color:var(--accent-lit); }
  .gp-modes{ display:flex; gap:6px; flex-wrap:wrap; padding:0 13px 10px; }
  .gp-mode{
    font-family:var(--pixel); font-size:calc(7px * var(--ui-scale));
    padding:10px 12px; cursor:pointer; color:var(--text-dim);
    background:var(--slot); border:2px solid var(--bezel);
  }
  .gp-mode.active{ background:var(--accent); color:var(--on-accent); }

  /* ---- Section nav: one band at a time, nothing to scroll past ---- */
  .nav{ gap:6px; }
  .nav button{
    font-family:var(--pixel); font-size:calc(7px * var(--ui-scale));
    color:var(--text-dim); cursor:pointer; padding:10px 12px;
    background:var(--slot); border:2px solid var(--bezel);
  }
  .nav button:hover{ color:var(--text); }
  .nav button.active{ background:var(--accent); color:var(--on-accent); }
  .section.hidden{ display:none; }

  /* ---- MIDI learn ---- */
  body.learning .ctl .name{ cursor:pointer; color:var(--warn); text-decoration:underline dotted; }
  body.learning .ctl .name:hover{ color:var(--accent-lit); }
  /* MPE lights the way MIDI Learn does when it is on. */
  #mpeSw.active{ color:var(--accent-lit); }
  .pw-msg{ margin:0 13px 10px; font-family:var(--pixel);
           font-size:calc(8px * var(--ui-scale)); line-height:1.6; }
  .pw-msg.ok{ color:var(--accent-lit); }
  .pw-msg.err{ color:var(--warn); }
  /* An unlocked switch pulses until first used: it appears in the chord
     matrix, a section away from the password box. */
  @keyframes unlockPulse{
    0%, 100% { box-shadow:0 0 0 0 var(--accent-lit); }
    50%      { box-shadow:0 0 0 4px var(--accent-lit); }
  }
  .switch.fresh{ animation:unlockPulse 1.2s ease-in-out infinite; }
  .ctl .name.armed{ color:var(--accent-lit) !important; }
  .ctl .cc{
    font-family:var(--pixel); font-size:calc(6px * var(--ui-scale));
    color:var(--text-dim); margin-left:6px; opacity:.75;
  }

  /* ---- Section bands ---- */
  .section{ margin-bottom:22px; }
  .section-head{
    display:flex; align-items:baseline; gap:12px; flex-wrap:wrap;
    border-left:5px solid var(--accent); padding:2px 0 2px 11px; margin-bottom:5px;
  }
  .section-head h2{
    font-family:var(--pixel); font-size:calc(11px * var(--ui-scale));
    margin:0; color:var(--text); text-shadow:var(--glow);
  }
  .section-head .scope{
    font-family:var(--pixel); font-size:calc(7px * var(--ui-scale));
    color:var(--on-accent); background:var(--accent); padding:4px 7px;
  }
  .section-blurb{
    color:var(--text-dim); font-size:calc(11.5px * var(--ui-scale));
    line-height:1.6; margin:0 0 11px 16px; max-width:76ch;
  }
  /* Warp spans both voice types, so it spans the grid too. */
  .section.warp .section-head{ border-left-color:var(--warn); }
  .section.warp .section-head .scope{ background:var(--warn); color:var(--on-accent); }
  .section.warp .modules{ grid-template-columns:1fr; }
  .section.warp .module h2{ background:var(--warn); color:var(--on-accent); }

  .modules{ display:grid; grid-template-columns:repeat(auto-fill,minmax(285px,1fr)); gap:14px; }
  .module{
    background:linear-gradient(180deg, var(--body) 0%, var(--body-dark) 100%);
    border:2px solid var(--bezel);
    box-shadow: inset 0 2px 0 var(--body-lit), inset 0 -2px 0 rgba(0,0,0,.55);
    padding:0 0 14px;
  }
  .module h2{
    font-family:var(--pixel); font-size:calc(8px * var(--ui-scale));
    letter-spacing:.04em; margin:0 0 13px; padding:11px 12px; line-height:1.5;
    color:var(--on-accent); background:var(--accent);
    border-bottom:2px solid var(--bezel); text-shadow:1px 1px 0 rgba(0,0,0,.25);
  }
  /* Warp's own controls sit in a row rather than a column, since it is wide */
  .section.warp .module .ctl{ display:inline-block; width:min(260px,100%); vertical-align:top; margin-right:18px; }

  .ctl{ margin:0 13px 14px; }
  .ctl:last-child{ margin-bottom:0; }
  .ctl .row{ display:flex; justify-content:space-between; align-items:center; gap:10px; margin-bottom:7px; }
  .ctl .name{
    font-family:var(--pixel); font-size:calc(7px * var(--ui-scale));
    color:var(--text-dim); line-height:1.5;
  }
  .ctl .value{
    font-size:calc(12px * var(--ui-scale)); font-weight:700;
    color:var(--accent-lit); text-shadow:var(--glow);
  }
  .ctl .help{
    font-size:calc(10.5px * var(--ui-scale)); color:var(--text-dim);
    margin-top:6px; line-height:1.5;
  }

  .switch{
    width:34px; height:34px; border-radius:50%; flex:none; cursor:pointer;
    background:radial-gradient(circle at 38% 32%, var(--body-lit) 0%, var(--body-dark) 70%);
    border:2px solid var(--bezel); box-shadow: inset 0 -2px 3px rgba(0,0,0,.6);
    display:flex; align-items:center; justify-content:center;
  }
  .switch .led{ width:9px; height:9px; border-radius:50%; background:var(--bezel); transition:background .12s, box-shadow .12s; }
  .switch.active{ background:radial-gradient(circle at 38% 32%, var(--accent-lit) 0%, var(--accent) 72%); }
  .switch.active .led{ background:#fff; box-shadow:0 0 8px var(--accent-lit); }

  input[type=range]{ -webkit-appearance:none; appearance:none; width:100%; height:20px; background:transparent; cursor:pointer; margin:0; }
  input[type=range]::-webkit-slider-runnable-track{ height:8px; background:var(--slot); border:2px solid var(--bezel); }
  input[type=range]::-webkit-slider-thumb{
    -webkit-appearance:none; width:14px; height:18px; margin-top:-7px;
    background:linear-gradient(180deg, var(--body-lit) 0%, var(--body-dark) 100%);
    border:2px solid var(--bezel);
  }
  input[type=range]:hover::-webkit-slider-thumb{ background:linear-gradient(180deg, var(--accent-lit) 0%, var(--accent) 100%); }
  input[type=range]::-moz-range-track{ height:8px; background:var(--slot); border:2px solid var(--bezel); }
  input[type=range]::-moz-range-thumb{ width:14px; height:18px; border-radius:0; background:var(--body-lit); border:2px solid var(--bezel); }

  .enum-row{ display:flex; gap:5px; flex-wrap:wrap; }
  .enum-btn{
    font-family:var(--pixel); font-size:calc(7px * var(--ui-scale)); line-height:1.5;
    background:var(--slot); color:var(--text-dim);
    border:2px solid var(--bezel); padding:8px; cursor:pointer;
  }
  .enum-btn:hover{ color:var(--text); }
  .enum-btn.active{ background:var(--accent); color:var(--on-accent); text-shadow:none; }

  .console{ margin-top:16px; background:var(--slot); border:2px solid var(--bezel); padding:12px 13px; }
  .console-head{ display:flex; justify-content:space-between; align-items:center; margin-bottom:9px; }
  .console-head .label{ font-family:var(--pixel); font-size:calc(7px * var(--ui-scale)); color:var(--text-dim); }
  .console .clear{ font-family:var(--pixel); font-size:calc(7px * var(--ui-scale)); color:var(--text-dim); background:none; border:none; cursor:pointer; }
  .console .clear:hover{ color:var(--accent-lit); }
  .log{ height:122px; overflow-y:auto; font-size:calc(11.5px * var(--ui-scale)); line-height:1.65; color:var(--text-dim); }
  .log .tx{ color:var(--ok); }
  .log .rx{ color:var(--warn); }
  .log .sys{ color:var(--text-dim); font-style:italic; }
  .log .err{ color:var(--accent-lit); }

  footer{
    text-align:center; color:var(--text-dim); font-family:var(--pixel);
    font-size:calc(7px * var(--ui-scale)); line-height:1.9; margin-top:20px;
  }

  @media (prefers-reduced-motion: reduce){ *{ transition:none !important; } }
  @media (max-width:560px){
    .brand h1{ font-size:calc(15px * var(--ui-scale)); }
    .head-inner{ padding:14px; }
  }
</style>
__EXTRA_HEAD__
<link rel="icon" type="image/svg+xml" href="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">
<link rel="icon" type="image/png" sizes="32x32" href="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">
</head>
<body>
<div class="rack">

  <header>
    <div class="stripe"><i></i><i></i><i></i><i></i><i></i></div>
    <div class="head-inner">
      <div class="brand">
        <div class="eyebrow">__BRAND__</div>
        <h1>8-BIT<br>8ASTERD <span>&#9632;</span></h1>
        <p>__INTRO__</p>
      </div>
      <div class="connection">
        <div class="status-pill" id="statusPill"><span class="dot"></span><span id="statusText">Disconnected</span></div>
__TRANSPORT_UI__
      </div>
    </div>
  </header>

  <div class="unsupported" id="unsupported" style="display:none;">
    <b>Web Serial isn't available here.</b> This panel needs Chrome or Edge (desktop),
    opened as a local file — Safari and Firefox don't implement the Web Serial API yet.
  </div>

  <div class="mismatch" id="mismatch" style="display:none;">
    <b>Firmware doesn't match this panel.</b>
    <span id="mismatchDetail"></span>
    Re-run <code>generate.py</code>, then recompile and re-flash. Until you do,
    every control here writes to the wrong parameter on the unit.
  </div>

  <div class="transport" id="transport">
    <button class="btn play" id="seqPlay">Play</button>
    <span class="tinfo" id="transportInfo">&mdash;</span>
    <span class="spacer"></span>
    <button class="btn" id="imgSave">Save Game</button>
    <input type="file" id="imgLoadInput" accept=".8b8,.json" style="display:none">
    <button class="btn" id="imgLoad">Load Game</button>
  </div>

  <div class="bar">
    <button class="btn" id="settingsBtn">Settings</button>
    <span class="spacer"></span>
    <button class="btn" id="mpeSw">MPE</button>
    <button class="btn" id="learnBtn">MIDI Learn</button>
    <button class="btn" id="diagBtn">Diag</button>
  </div>

  <div class="bar settings" id="settingsPanel" hidden>
    <span class="label">Theme</span>
    <select id="themeSelect">
      <option value="nes">NES</option>
      <option value="arcade">Arcade</option>
      <option value="handheld">Handheld</option>
    </select>
    <span class="label">Text</span>
    <select id="sizeSelect">
      <option value="0.85">Small</option>
      <option value="1" selected>Normal</option>
      <option value="1.2">Large</option>
      <option value="1.45">Larger</option>
    </select>
    <span class="label">Detail</span>
    <select id="detailSelect">
      <option value="full">Full</option>
      <option value="compact">Compact</option>
    </select>
  </div>

  <nav class="bar nav" id="nav"></nav>

  <div class="bar presets">
    <span class="label">Preset</span>
    <select id="presetSelect"></select>
    <button class="btn" id="applyPreset">Apply</button>
    <button class="btn" id="readUnit">Read Unit</button>
    <button class="btn" id="saveUnit">Save to Unit</button>
    <button class="btn" id="defaultsBtn">Defaults</button>
    <button class="btn" id="exportBtn">Export</button>
    <button class="btn" id="importBtn">Import</button>
  </div>

  <div id="sections"></div>


  <section class="section" id="playSection">
    <div class="section-head">
      <h2>Play</h2><span class="scope">chords + harp</span>
    </div>
    <p class="section-blurb">Seven roots around the circle of fifths, three chord types, and a strumpad whose twelve notes follow whatever chord is held. Works with a mouse, a finger, or the letter keys.</p>
    <div class="module">
      <h2>Chord Matrix</h2>
      <div class="cc-row">
        <div class="cc">
          <div class="switch" id="sharpSw"><div class="led"></div></div>
          <span class="cc-label">Sharp</span>
        </div>
        <div class="cc">
          <div class="switch" id="latchSw"><div class="led"></div></div>
          <span class="cc-label">Hold</span>
        </div>
        <div class="cc">
          <div class="switch" id="barrySw"><div class="led"></div></div>
          <span class="cc-label">Barry</span>
        </div>
        <div class="cc" id="septCell" hidden>
          <div class="switch" id="septSw"><div class="led"></div></div>
          <span class="cc-label">Septimal</span>
        </div>
        <div class="cc">
          <select id="chordLayoutSel">
            <option value="0">Standard</option>
            <option value="1">Alternate</option>
          </select>
          <span class="cc-label">Layout</span>
        </div>
        <div class="cc">
          <div class="switch" id="stackSw"><div class="led"></div></div>
          <span class="cc-label">Stack</span>
        </div>
        <div class="cc">
          <select id="harpModeSel"></select>
          <span class="cc-label">Harp</span>
        </div>
        <div class="cc">
          <select id="keySigSel"></select>
          <span class="cc-label">Key</span>
        </div>
        <div class="cc">
          <select id="accModeSel">
            <option value="0">Follow key</option>
            <option value="1">Sharp</option>
            <option value="2">Flat</option>
          </select>
          <span class="cc-label">Accidental</span>
        </div>
        <div class="cc">
          <select id="strumDirSel">
            <option value="v">Vertical</option>
            <option value="h">Horizontal</option>
            <option value="grid">Grid</option>
          </select>
          <span class="cc-label">Layout</span>
        </div>
        <div class="cc">
          <div class="oct" id="chordOct"></div>
          <span class="cc-label">Chord 8ve</span>
        </div>
        <div class="cc">
          <div class="oct" id="strumOct"></div>
          <span class="cc-label">Strum 8ve</span>
        </div>
        <div class="cc">
          <select id="inversionSel">
            <option value="0">Root</option>
            <option value="1">1st</option>
            <option value="2">2nd</option>
            <option value="3">3rd</option>
          </select>
          <span class="cc-label">Inversion</span>
        </div>
        <div class="cc">
          <select id="spacingSel">
            <option value="0">Close</option>
            <option value="1">Drop 2</option>
            <option value="2">Drop 3</option>
            <option value="3">Drop 2+4</option>
            <option value="4">Spread</option>
          </select>
          <span class="cc-label">Spacing</span>
        </div>
        <div class="cc">
          <span class="readout" id="chordName">&mdash;</span>
          <span class="cc-label">Playing</span>
        </div>
      </div>

      <div class="play-wrap">
        <div class="matrix">
          <div class="cols" id="colHeads"></div>
          <div class="cols" id="chordGrid"></div>
        </div>
        <div class="strum" id="strum"></div>
      </div>
    </div>

    <div class="module">
      <h2>Keyboard</h2>
      <div class="cc-row">
        <div class="cc">
          <div class="oct" id="kbOct"></div>
          <span class="cc-label">Octave</span>
        </div>
        <div class="cc">
          <span class="readout" id="kbRange">C4 &ndash; B5</span>
          <span class="cc-label">Range</span>
        </div>
        <div class="cc">
          <span class="readout" id="midiStatus">none</span>
          <span class="cc-label">MIDI In</span>
        </div>
      </div>
      <div class="piano-scroll"><div class="piano" id="piano"></div></div>
      <div class="pads" id="pads"></div>
    </div>
  </section>

  <section class="section" id="seqSection">
    <div class="section-head">
      <h2>Sequencer</h2><span class="scope">16 steps</span>
    </div>
    <p class="section-blurb">Sixteen steps of drums. Tap the row name to audition a sound. Everything the Drums and Drum FX sections do applies while it runs, so this is the quickest way to hear what Roll, Chaos or a Warp mode actually do to a pattern.</p>
    <div class="module">
      <h2>Drum Sequencer</h2>
      <div class="cc-row">
        <div class="cc">
          <select id="seqPreset"></select>
          <span class="cc-label">Pattern</span>
        </div>
        <div class="cc">
          <select id="seqPageSel">
            <option value="0">1&ndash;16</option>
            <option value="1">17&ndash;32</option>
            <option value="2">33&ndash;48</option>
            <option value="3">49&ndash;64</option>
          </select>
          <span class="cc-label">Page</span>
        </div>
        <div class="cc">
          <select id="seqLen"></select>
          <span class="cc-label">Length</span>
        </div>
        <div class="cc">
          <select id="seqSig">
            <option value="4">4/4</option>
            <option value="3">3/4</option>
            <option value="6">6/8</option>
            <option value="5">5/4</option>
            <option value="7">7/8</option>
          </select>
          <span class="cc-label">Signature</span>
        </div>
        <div class="cc">
          <input type="range" id="seqTempo" min="50" max="200" value="110"
                 style="width:150px">
          <span class="cc-label" id="seqBpm">110 BPM</span>
        </div>
        <div class="cc">
          <input type="range" id="seqSwing" min="0" max="66" value="0"
                 style="width:110px">
          <span class="cc-label" id="seqSwingVal">Swing 0%</span>
        </div>
        <div class="cc">
          <button class="btn" id="seqTap">Tap</button>
          <span class="cc-label">Tempo</span>
        </div>
        <div class="cc">
          <button class="btn" id="seqClear">Clear</button>
          <span class="cc-label">This page</span>
        </div>
        <div class="cc">
          <select id="seqCopyTo">
            <option value="0">1&ndash;16</option>
            <option value="1">17&ndash;32</option>
            <option value="2">33&ndash;48</option>
            <option value="3">49&ndash;64</option>
          </select>
          <span class="cc-label">Copy to</span>
        </div>
        <div class="cc">
          <button class="btn" id="seqCopyBtn">Copy</button>
          <span class="cc-label">Page</span>
        </div>
      </div>

      <div class="seq">
        <div class="seqhead" id="seqHead"></div>
        <div id="seqRows"></div>
      </div>
    </div>

    <div class="module">
      <h2>Password</h2>
      <div class="bar cc-row" style="margin:0 13px 10px;align-items:flex-end;">
        <div class="cc">
          <input type="text" id="pwInput" placeholder="ENTER CODE"
                 spellcheck="false" style="width:220px;font-family:var(--mono)">
          <span class="cc-label">Enter</span>
        </div>
        <div class="cc">
          <button class="btn" id="pwGo">Go</button>
          <span class="cc-label">Load patch</span>
        </div>
        <span class="spacer"></span>
        <div class="cc">
          <input type="text" id="pwShow" readonly placeholder="—"
                 style="width:220px;font-family:var(--mono)">
          <span class="cc-label">This patch</span>
        </div>
        <div class="cc">
          <button class="btn" id="pwMake">Make</button>
          <span class="cc-label">Generate</span>
        </div>
      </div>
      <p class="pw-msg" id="pwMsg" hidden></p>
      <p class="section-blurb">A password carries the settings alone &mdash; short enough to read aloud or print on a card. Save Game carries everything else.</p>
    </div>

    <div class="module">
      <h2>MIDI File</h2>
      <div class="bar filepick cc-row" style="margin:0 13px 10px;align-items:flex-end;">
        <input type="file" id="midiFileInput" accept=".mid,.midi,audio/midi">
        <label for="midiFileInput">Choose .mid</label>
        <span class="fname" id="midiFileName">no file</span>
        <span class="spacer"></span>
        <div class="cc">
          <input type="range" id="midiSpeed" min="25" max="200" value="100"
                 style="width:150px">
          <span class="cc-label" id="midiSpeedVal">Speed 1.00x</span>
        </div>
        <div class="cc">
          <div class="switch" id="midiLoopSw"><div class="led"></div></div>
          <span class="cc-label">Loop</span>
        </div>
        <div class="cc">
          <div class="switch" id="midiSyncSw"><div class="led"></div></div>
          <span class="cc-label">Sync tempo</span>
        </div>
        <div class="cc">
          <button class="btn" id="midiPlayBtn">Play File</button>
          <span class="cc-label">Playback</span>
        </div>
      </div>
      <p class="section-blurb" id="midiFileInfo">No file loaded. Channel 10 plays the drum kit; every other channel goes to the tone voices, so every setting on this panel shapes the playback &mdash; temperament, envelope, unison, the Warp Zone, all of it.</p>
    </div>

    <div class="module">
      <h2>Note Sequencer</h2>
      <div class="cc-row">
        <div class="cc">
          <div class="oct" id="noteOct"></div>
          <span class="cc-label">Octave</span>
        </div>
        <div class="cc">
          <span class="readout" id="noteRange">C3 &ndash; B3</span>
          <span class="cc-label">Range</span>
        </div>
      </div>
      <div class="seq">
        <div id="noteRows"></div>
      </div>
    </div>
  </section>


  <section class="section" id="gamepadSection">
    <div class="section-head">
      <h2>Gamepad</h2><span class="scope">bluetooth pad</span>
    </div>
    <p class="section-blurb">Connect a Bluetooth controller and press any button to wake it up. Three modes, cycled with Select or the buttons below. The right stick always strums whatever chord is held.</p>
    <div class="module">
      <h2>Controller</h2>
      <div class="gp-modes" id="gpModes"></div>
      <div class="gp-live" id="gpLive">No controller detected. Pair it, then press a button.</div>
      <div class="gp-grid" id="gpAssign"></div>
    </div>
  </section>

__EXTRA_BODY__

  <div class="console">
    <div class="console-head">
      <span class="label">Serial Log</span>
      <button class="clear" id="clearLog">Clear</button>
    </div>
    <div class="log" id="log"></div>
  </div>

  <footer><a href="https://keyandcable.com/projects.html" target="_blank" rel="noopener" style="color:inherit;text-decoration:none">THE KEY &amp; CABLE COMPANY</a> &#9632; <a href="https://keyandcable.com/thanks.html" target="_blank" rel="noopener" style="color:inherit">SAY THANKS</a></footer>
</div>

<script>
/* ==== Generated data ==================================================== */
const PARAMS  = __PARAMS_JSON__;
const PRESETS = __PRESETS_JSON__;
const NUM_PARAMS = __NUM_PARAMS__;
const LAYOUT_VERSION = __LAYOUT_VERSION__;
const SECTIONS = __SECTIONS_JSON__;  // must match the flashed firmware

/* ==== State ============================================================= */
const values = PARAMS.map(p => p.default);

/* ==== Logging =========================================================== */
const logEl = document.getElementById('log');
function log(cls, text){
  const row = document.createElement('div');
  row.className = cls; row.textContent = text;
  logEl.appendChild(row);
  logEl.scrollTop = logEl.scrollHeight;
  while (logEl.children.length > 300) logEl.removeChild(logEl.firstChild);
}
document.getElementById('clearLog').onclick = () => { logEl.innerHTML = ''; };

__TRANSPORT_JS__

/* ==== Protocol (shared by both transports) ============================== */
let sawLayout = false;

function handleLine(line){
  if (line.startsWith('PRESET:')){
    log('rx','\u00ab ' + line);
    const vals = line.slice(7).split(',').map(v => parseInt(v, 10));
    for (let i = 0; i < Math.min(vals.length, NUM_PARAMS); i++){
      if (!isNaN(vals[i])) values[i] = vals[i];
    }
    renderAll();
  }
  else if (line.startsWith('V:')){
    log('rx','\u00ab ' + line);
    const [, i, v] = line.split(':');
    const idx = parseInt(i, 10), val = parseInt(v, 10);
    if (idx >= 0 && idx < NUM_PARAMS && !isNaN(val)){
      values[idx] = val;
      renderOne(idx);
    }
  }
  else if (line.startsWith('LAYOUT:')){
    log('rx','\u00ab ' + line);
    const [vStr, cStr] = line.slice(7).split(',');
    const fwVer   = parseInt(vStr, 16);
    const fwCount = parseInt(cStr, 10);
    sawLayout = true;
    const ok = (fwVer === LAYOUT_VERSION && fwCount === NUM_PARAMS);
    const box = document.getElementById('mismatch');
    if (ok){
      box.style.display = 'none';
      log('sys', 'Firmware layout 0x' + fwVer.toString(16).toUpperCase() +
                 ' with ' + fwCount + ' parameters \u2014 matches this panel.');
    } else {
      document.getElementById('mismatchDetail').textContent =
        'The unit reports layout 0x' + (isNaN(fwVer) ? '??' : fwVer.toString(16).toUpperCase()) +
        ' with ' + fwCount + ' parameters; this panel was generated for layout 0x' +
        LAYOUT_VERSION.toString(16).toUpperCase() + ' with ' + NUM_PARAMS + '.';
      box.style.display = 'block';
      log('err', 'LAYOUT MISMATCH \u2014 the flashed firmware is not this version.');
    }
  }
  else if (line.startsWith('RAM:')){
    // free-now : closest-the-stack-has-ever-come, both in bytes
    const [, now, low] = line.split(':');
    const n = parseInt(now, 10), l = parseInt(low, 10);
    if (isNaN(n) || n < 0){
      log('sys', 'RAM: not measured (emulator uses the host stack)');
    } else {
      const verdict = l < 128 ? '  <-- TIGHT, stack has come close'
                    : l < 256 ? '  (getting close)' : '  (comfortable)';
      log(l < 128 ? 'err' : 'sys',
          'RAM free now ' + n + ' bytes, closest ever ' + l + verdict);
    }
  }
  else if (line.startsWith('DIAG')){
    log('rx','\u00ab ' + line);
  }
  else if (line.startsWith('CCMAP:')){
    log('rx','\u00ab ' + line);
    line.slice(6).split(',').forEach((v, i) => { ccAssign[i] = parseInt(v, 10); });
    renderCc();
  }
  else if (line.startsWith('CC:')){
    log('rx','\u00ab ' + line);
    const parts = line.split(':');
    ccAssign[parseInt(parts[1], 10)] = parseInt(parts[2], 10);
    document.querySelectorAll('.ctl .name.armed').forEach(e => e.classList.remove('armed'));
    renderCc();
  }
  else if (line.startsWith('LEARNING:')){
    log('sys','Waiting for a CC \u2014 move a control on your MIDI controller.');
  }
  else if (line.startsWith('ERR:')){
    // The unit rejected a command rather than half-applying it.
    log('err','\u00ab ' + line);
    if (line.startsWith('ERR:LONG')){
      log('err','A command was too long for the unit and was ignored. ' +
                'Firmware and panel are out of step \u2014 reflash.');
    } else if (line.startsWith('ERR:SHORT')){
      log('err','The preset had fewer values than the unit expects. ' +
                'Re-run generate.py and reflash.');
    }
  }
  else if (line.startsWith('SAVED:')){
    log('rx','\u00ab ' + line);
    log('sys','Parameters saved to the unit\u2019s EEPROM.');
  }
  // Anything else (e.g. DEBUG output sharing the port) is ignored.
}

/* ==== Sending param changes ============================================ */
function throttle(fn, ms){
  let last = 0, pending = null;
  return (...args) => {
    const now = Date.now();
    if (now - last >= ms){ last = now; fn(...args); }
    else{
      clearTimeout(pending);
      pending = setTimeout(() => { last = Date.now(); fn(...args); }, ms - (now - last));
    }
  };
}
const throttledSend = PARAMS.map(p => throttle(v => send('P:' + p.index + ':' + v), 70));

function setValue(idx, v, flush){
  values[idx] = v;
  renderOne(idx);
  if (flush) send('P:' + idx + ':' + v);
  else throttledSend[idx](v);
}

/* ==== UI construction =================================================== */
function displayText(p, raw){
  const shown = (raw + p.offset) * p.scale;
  const txt = (p.scale < 1) ? shown.toFixed(1) : String(shown);
  return p.unit ? txt + ' ' + p.unit : txt;
}

const renderers = [];  // index -> function updating that control's visuals

function buildUI(){
  const host = document.getElementById('sections');
  const seen = new Set();

  for (const sec of SECTIONS){
    const groups = sec.groups.filter(g => PARAMS.some(p => p.group === g));
    if (!groups.length) continue;

    const band = document.createElement('section');
    band.className = 'section ' + sec.key;

    const head = document.createElement('div');
    head.className = 'section-head';
    const h = document.createElement('h2'); h.textContent = sec.title;
    const sc = document.createElement('span'); sc.className = 'scope'; sc.textContent = sec.scope;
    head.appendChild(h); head.appendChild(sc);
    band.appendChild(head);

    if (sec.blurb){
      const bl = document.createElement('p');
      bl.className = 'section-blurb'; bl.textContent = sec.blurb;
      band.appendChild(bl);
    }

    const mods = document.createElement('div');
    mods.className = 'modules';
    for (const g of groups){
      seen.add(g);
      const mod = document.createElement('section');
      mod.className = 'module';
      const mh = document.createElement('h2'); mh.textContent = g;
      mod.appendChild(mh);
      for (const p of PARAMS.filter(x => x.group === g)) mod.appendChild(buildControl(p));
      mods.appendChild(mod);
    }
    band.appendChild(mods);
    host.appendChild(band);
  }

  // Anything a new parameter group introduced without a section still shows,
  // rather than silently vanishing from the panel.
  const orphans = [...new Set(PARAMS.map(p => p.group))].filter(g => !seen.has(g));
  if (orphans.length){
    const mods = document.createElement('div');
    mods.className = 'modules';
    for (const g of orphans){
      const mod = document.createElement('section');
      mod.className = 'module';
      const mh = document.createElement('h2'); mh.textContent = g;
      mod.appendChild(mh);
      for (const p of PARAMS.filter(x => x.group === g)) mod.appendChild(buildControl(p));
      mods.appendChild(mod);
    }
    host.appendChild(mods);
  }

  const sel = document.getElementById('presetSelect');
  for (const name of Object.keys(PRESETS)){
    const o = document.createElement('option');
    o.value = name; o.textContent = name;
    sel.appendChild(o);
  }
}

function buildControl(p){
  const wrap = document.createElement('div');
  wrap.className = 'ctl';

  const row = document.createElement('div');
  row.className = 'row';
  const name = document.createElement('span');
  name.className = 'name'; name.textContent = p.label;
  const ccTag = document.createElement('span');
  ccTag.className = 'cc'; ccTag.dataset.idx = p.index;
  name.appendChild(ccTag);
  // In learn mode the label is the target: click it, then move something on
  // the controller and the firmware binds whatever CC that sent.
  name.onclick = () => {
    if (!document.body.classList.contains('learning')) return;
    document.querySelectorAll('.ctl .name.armed').forEach(e => e.classList.remove('armed'));
    name.classList.add('armed');
    send('LEARN:' + p.index);
  };
  row.appendChild(name);
  wrap.appendChild(row);

  if (p.kind === 'toggle'){
    const sw = document.createElement('div');
    sw.className = 'switch';
    sw.innerHTML = '<div class="led"></div>';
    sw.onclick = () => setValue(p.index, values[p.index] ? 0 : 1, true);
    row.appendChild(sw);
    renderers[p.index] = () => sw.classList.toggle('active', !!values[p.index]);
  }
  else if (p.kind === 'enum'){
    const er = document.createElement('div');
    er.className = 'enum-row';
    p.options.forEach((label, oi) => {
      const b = document.createElement('button');
      b.className = 'enum-btn'; b.textContent = label;
      b.onclick = () => setValue(p.index, oi, true);
      er.appendChild(b);
    });
    wrap.appendChild(er);
    renderers[p.index] = () => {
      [...er.children].forEach((b, oi) =>
        b.classList.toggle('active', oi === values[p.index]));
    };
  }
  else{ // int slider
    const val = document.createElement('span');
    val.className = 'value';
    row.appendChild(val);
    const slider = document.createElement('input');
    slider.type = 'range';
    slider.min = p.min; slider.max = p.max; slider.step = 1;
    slider.oninput = () => setValue(p.index, parseInt(slider.value, 10), false);
    slider.onchange = () => setValue(p.index, parseInt(slider.value, 10), true);
    wrap.appendChild(slider);
    renderers[p.index] = () => {
      slider.value = values[p.index];
      val.textContent = displayText(p, values[p.index]);
    };
  }

  if (p.help){
    const help = document.createElement('div');
    help.className = 'help'; help.textContent = p.help;
    wrap.appendChild(help);
  }
  return wrap;
}

function renderOne(i){ renderers[i] && renderers[i](); }
function renderAll(){ for (let i = 0; i < NUM_PARAMS; i++) renderOne(i); }

/* ==== Preset actions ==================================================== */
document.getElementById('applyPreset').onclick = () => {
  const name = document.getElementById('presetSelect').value;
  const arr = PRESETS[name];
  if (!arr) return;
  for (let i = 0; i < NUM_PARAMS; i++) values[i] = arr[i];
  renderAll();
  send('LOAD:' + arr.join(','));
};
document.getElementById('readUnit').onclick = () => send('DUMP');
document.getElementById('saveUnit').onclick = () => send('SAVE');
document.getElementById('defaultsBtn').onclick = () => send('DEFAULTS');

document.getElementById('exportBtn').onclick = async () => {
  const json = JSON.stringify(values);
  try{
    await navigator.clipboard.writeText(json);
    log('sys','Current values copied to clipboard: ' + json);
  }catch(e){
    log('sys','Copy this preset: ' + json);
  }
};
document.getElementById('importBtn').onclick = () => {
  const text = prompt('Paste a preset array (e.g. [0,1,0,...]):');
  if (!text) return;
  try{
    const arr = JSON.parse(text);
    if (!Array.isArray(arr)) throw new Error('not an array');
    for (let i = 0; i < Math.min(arr.length, NUM_PARAMS); i++){
      values[i] = arr[i] | 0;
    }
    renderAll();
    send('LOAD:' + values.join(','));
  }catch(e){
    log('err','Import failed: ' + e.message);
  }
};

/* ==== Diagnostics ======================================================= */
// Diag asks the unit for its live voice map: what each of the 9 voices is
// doing, which chip it sits on, its ADSR stage and its age in ticks. That is
// the thing to read when notes choke.
document.getElementById('diagBtn').onclick = () => send('DIAG');


/* ==== Play surface ====================================================== */
// Layout follows the minichord: seven columns of roots around the circle of
// fifths, three rows for major / minor / 7th, and a sharp modifier that
// lifts every note a semitone. The strumpad is the harp -- twelve stacked
// sections whose notes come from the chord currently held.

const ROOTS  = [['F',53],['C',48],['G',55],['D',50],['A',57],['E',52],['B',59]];

// The columns are F C G D A E B, which is exactly the order sharps are added
// to a signature and the reverse of the order flats are. So a key signature
// falls onto the matrix in order: N sharps alter the first N columns, N flats
// the last N. Choosing a key therefore respells the whole matrix at once --
// in D you press the F button and get F# major.
const KEY_SIGS = [
  ['Cb', 11, -7], ['Gb',  6, -6], ['Db',  1, -5], ['Ab',  8, -4],
  ['Eb',  3, -3], ['Bb', 10, -2], ['F',   5, -1], ['C',   0,  0],
  ['G',   7,  1], ['D',   2,  2], ['A',   9,  3], ['E',   4,  4],
  ['B',  11,  5], ['F#',  6,  6], ['C#',  1,  7]
];
let keySig = 7;                      // index into KEY_SIGS; 7 is C major

// 0 = follow the signature (sharpen in sharp keys, flatten in flat keys),
// 1 = always sharpen, 2 = always flatten. Players do not all think of that
// button the same way, so it is not tied to the key unless asked.
let accidentalMode = 0;

function keyAlterations(){
  const n = KEY_SIGS[keySig][2];
  const alt = [0, 0, 0, 0, 0, 0, 0];
  if (n > 0) for (let i = 0; i < n; i++) alt[i] = 1;        // F C G D A E B
  else for (let i = 0; i < -n; i++) alt[6 - i] = -1;        // B E A D G C F
  return alt;
}

// What the sharp/flat button does right now: +1, -1, or nothing.
function modifierStep(){
  if (!sharpOn) return 0;
  if (accidentalMode === 1) return 1;
  if (accidentalMode === 2) return -1;
  return KEY_SIGS[keySig][2] < 0 ? -1 : 1;                  // follow the key
}

function accidentalText(a){
  return a === 0 ? '' : a === 1 ? '\u266f' : a === 2 ? '\u00d7'
       : a === -1 ? '\u266d' : a === -2 ? '\u266d\u266d' : '?';
}

// Column i's root: its letter plus whatever the key and the button say.
function rootAlter(i){ return keyAlterations()[i] + modifierStep(); }
function rootPc(i){ return ((ROOTS[i][1] + rootAlter(i)) % 12 + 12) % 12; }
function rootName(i){ return ROOTS[i][0] + accidentalText(rootAlter(i)); }
function rootMidi(i){ return ROOTS[i][1] + rootAlter(i); }
const QUALITY = [
  { suffix: '',  name: 'Maj' },
  { suffix: 'm', name: 'Min' },
  { suffix: '7', name: '7th' }
];

// Button combinations, following the minichord: a row can be pressed on its
// own or stacked with others in the same column. The key is the sorted set
// of held rows, so "0" is major alone and "02" is major plus 7th.
//
// barry: Barry Harris treats the major sixth and the diminished seventh as
// the two halves of one scale, so in that mode a major becomes a sixth, a
// minor becomes a minor sixth, and a diminished becomes a diminished
// seventh. The sevenths are already four-note chords and are left alone.
const CHORDS = {
  '0':   { tones: [0,4,7],    suffix: '',     barry: [0,4,7,9], bSuffix: '6'    },
  '1':   { tones: [0,3,7],    suffix: 'm',    barry: [0,3,7,9], bSuffix: 'm6'   },
  '2':   { tones: [0,4,7,10], suffix: '7'     },
  '01':  { tones: [0,3,6],    suffix: 'dim',  barry: [0,3,6,9], bSuffix: 'dim7' },
  '02':  { tones: [0,4,7,11], suffix: 'maj7'  },
  '12':  { tones: [0,3,7,10], suffix: 'm7'    },
  '012': { tones: [0,4,8],    suffix: 'aug'   }
};

// Septimal counterparts of the same seven chords, unlocked by a password.
// Each keeps the standard chord's notes where it can and moves them to 7-limit
// just ratios, given as cents from equal temperament per tone: the firmware
// has no pitch between the MIDI notes, so the panel sends these as a tuning
// table and the notes are retuned in place. That is what makes the comparison
// work: flip the switch under a held chord and only the tuning changes.
// The augmented slot has no septimal triad of its own, so it becomes the
// utonal seventh, the one chord here whose notes change.
const SEPT = {
  '0':   { tones: [0,4,7],    cents: [0, 35, 2],       name: 'supermajor',     ratio: '14:18:21' },
  '1':   { tones: [0,3,7],    cents: [0,-33, 2],       name: 'subminor',       ratio: '6:7:9' },
  '2':   { tones: [0,4,7,10], cents: [0,-14, 2,-31],   name: 'harmonic 7th',   ratio: '4:5:6:7' },
  '01':  { tones: [0,3,6],    cents: [0,-33,-17],      name: 'utonal',         ratio: '1/7:1/6:1/5' },
  '02':  { tones: [0,4,7,11], cents: [0, 35, 2, 37],   name: 'supermajor 7th', ratio: '14:18:21:27' },
  '12':  { tones: [0,3,7,10], cents: [0,-33, 2,-31],   name: 'subminor 7th',   ratio: '12:14:18:21' },
  '012': { tones: [0,3,6,10], cents: [0,-33,-17,-31],  name: 'utonal 7th',     ratio: '1/7:1/6:1/5:1/4' }
};
const SEPT_ROW_SHORT = ['sup', 'sub', 'h7'];
// ---- Harp modes -----------------------------------------------------------
// Follows the scale modes I wrote for the minichord (upstream PR #125). The
// chord mode is the original behaviour: the strings ARE the chord, which is
// ideal for arpeggios but leaves nothing to play against it. The scale modes
// change what the strings are, so you can run up and down them freely while
// the chords move underneath and never land on a wrong note.
const SCALES = {
  ionian:      [0,2,4,5,7,9,11],
  lydian:      [0,2,4,6,7,9,11],
  mixolydian:  [0,2,4,5,7,9,10],
  dorian:      [0,2,3,5,7,9,10],
  aeolian:     [0,2,3,5,7,8,10],
  harmMinor:   [0,2,3,5,7,8,11],
  octatonic:   [0,2,3,5,6,8,9,11],   // whole-half, fits a diminished chord
  wholeTone:   [0,2,4,6,8,10],
  majSixthDim: [0,2,4,5,7,8,9,11],   // Barry Harris major sixth diminished
  minSixthDim: [0,2,3,5,7,8,9,11],   // and its minor counterpart
  majPent:     [0,2,4,7,9],
  minPent:     [0,3,5,7,10],
  domPent:     [0,2,4,7,10],
  dimPent:     [0,3,6,9,10]
};

// Mode 8: the mapping a jazz player would use, chosen from the chord type and
// rooted on the chord's own root rather than the key.
const CHORD_SCALE = {
  '0':   'ionian',     '02':  'lydian',   '2':   'mixolydian',
  '12':  'dorian',     '1':   'aeolian',  '01':  'octatonic',
  '012': 'wholeTone'
};
// The alternate layout: a second reading of the same three buttons, from the
// minichord's assignable chord layout (upstream PR #130). Three buttons give
// seven combinations and the standard set already uses all of them, so sus
// and extended chords need a second reading rather than new buttons. These
// are that feature's defaults. The ninth chords drop their fifth -- four
// voices, and that is how a player would voice them anyway.
const ALT_CHORDS = {
  '0':   { tones: [0,5,7],     suffix: 'sus4'  },
  '1':   { tones: [0,2,7],     suffix: 'sus2'  },
  '2':   { tones: [0,5,7,10],  suffix: '7sus4' },
  '02':  { tones: [0,4,11,14], suffix: 'maj9'  },
  '12':  { tones: [0,3,10,14], suffix: 'm9'    },
  '01':  { tones: [0,4,7,14],  suffix: 'add9'  },
  '012': { tones: [0,4,9,14],  suffix: '6/9'   }
};
const ALT_ROW_SUFFIX = ['sus4', 'sus2', '7sus4'];
const CHORD_SCALE_ALT = {
  '0': 'mixolydian', '1': 'ionian',  '2': 'mixolydian',
  '02': 'ionian',    '12': 'dorian', '01': 'ionian', '012': 'ionian'
};
let altLayout = false;

const CHORD_SCALE_BARRY = { '0': 'majSixthDim', '1': 'minSixthDim', '01': 'octatonic' };
// Mode 9: the same idea with pentatonics, which removes the semitones.
const CHORD_PENT = {
  '0':   'majPent',  '02': 'majPent', '2':   'domPent',
  '12':  'minPent',  '1':  'minPent', '01':  'dimPent',
  '012': 'wholeTone'
};

// Modes 1-7 ignore the chord and sit on the key. The "relative" ones root on
// the relative minor, nine semitones up.
const HARP_MODES = [
  { name: 'Chord tones',      kind: 'chord'                                  },
  { name: 'Major',            kind: 'key',  scale: 'ionian'                  },
  { name: 'Major pentatonic', kind: 'key',  scale: 'majPent'                 },
  { name: 'Minor pentatonic', kind: 'key',  scale: 'minPent'                 },
  { name: 'Diminished 6th',   kind: 'key',  scale: 'majSixthDim'             },
  { name: 'Rel. nat. minor',  kind: 'key',  scale: 'aeolian',   offset: 9    },
  { name: 'Rel. harm. minor', kind: 'key',  scale: 'harmMinor', offset: 9    },
  { name: 'Rel. min. pent.',  kind: 'key',  scale: 'minPent',   offset: 9    },
  { name: 'Scale per chord',  kind: 'perChord'                               },
  { name: 'Pentatonic/chord', kind: 'perChordPent'                           },
  { name: 'Custom on key',    kind: 'customKey'                              },
  { name: 'Custom on chord',  kind: 'customChord'                            }
];

const DEGREE_NAMES = ['1','b2','2','b3','3','4','b5','5','b6','6','b7','7'];

let harpMode = 0;
let customMask = 0b101010110101;       // a major scale to start from
let strumHorizontal = false;
let strumLayout = 'v';                 // v | h | grid

// Chord tones give four notes an octave, so twelve strings cover three
// octaves. A seven-note scale would only reach a octave and a half in twelve,
// so the scale modes get twenty-four and land in much the same range.
function strumCount(){ return HARP_MODES[harpMode].kind === 'chord' ? 12 : 24; }

// Returns { tones, root } -- the interval list and the pitch class it starts
// from, which is the chord root in some modes and the key in others.
function harpKeyFor(){ return currentKey() || lastHarpKey; }

function harpScaleFor(){
  const m = HARP_MODES[harpMode];
  const spec = chordSpec();
  const chordRoot = rootPc(activeRoot);

  if (m.kind === 'chord'){
    // Fall back to the last chord so the harp keeps its strings once the
    // button is released. No padding: this mode means the chord's own notes,
    // and a triad padded with a sixth put an E in a G major harp.
    const sp = spec || specForKey(lastHarpKey);
    if (!sp) return null;
    return { tones: sp.tones, root: chordRoot };
  }
  if (m.kind === 'key'){
    return { tones: SCALES[m.scale], root: (KEY_SIGS[keySig][1] + (m.offset || 0)) % 12 };
  }
  if (m.kind === 'perChord' || m.kind === 'perChordPent'){
    const key = harpKeyFor();
    if (!key) return null;
    const table = altLayout ? CHORD_SCALE_ALT
                : m.kind === 'perChordPent' ? CHORD_PENT
                : (barryOn && CHORD_SCALE_BARRY[key] ? CHORD_SCALE_BARRY : CHORD_SCALE);
    const name = table[key] || CHORD_SCALE[key] || 'ionian';
    return { tones: SCALES[name], root: chordRoot };
  }
  // Custom: a twelve bit mask, one bit per chromatic degree.
  const tones = [];
  for (let i = 0; i < 12; i++) if (customMask & (1 << i)) tones.push(i);
  if (!tones.length) return null;
  return { tones, root: m.kind === 'customKey' ? KEY_SIGS[keySig][1] : chordRoot };
}

let sharpOn = false, latchOn = false, barryOn = false, stackOn = false;
let septOn = false, septUnlocked = false;
let gestureRows = null;   // rows added by the current press-and-drag
let chordOct = 0, strumOct = 0, kbOct = 0;
let inversion = 0, spacing = 0;

// A small -/+ stepper. Limits differ per control because each sits at a
// different height in the firmware's MIDI 24..96 note table, and a setting
// that just gets folded back in looks like a broken button.
function makeOctave(id, get, set, lo, hi){
  const host = document.getElementById(id);
  if (!host) return () => {};
  const minus = document.createElement('button'); minus.textContent = '\u2212';
  const read  = document.createElement('span');
  const plus  = document.createElement('button'); plus.textContent = '+';
  host.appendChild(minus); host.appendChild(read); host.appendChild(plus);

  function show(){
    const v = get();
    read.textContent = v > 0 ? ('+' + v) : String(v);
  }
  function bump(d){
    const v = Math.max(lo, Math.min(hi, get() + d));
    set(v);
    try { localStorage.setItem('8b8.' + id, v); } catch(e){}
    show();
  }
  minus.onclick = () => bump(-1);
  plus.onclick  = () => bump(1);
  try {
    const saved = localStorage.getItem('8b8.' + id);
    if (saved !== null) set(Math.max(lo, Math.min(hi, parseInt(saved, 10) || 0)));
  } catch(e){}
  show();
  return show;
}
let activeRoot = 1;               // column currently selected
let heldRows = new Set();         // rows physically held right now
// What is actually sounding, which is not the same thing: with Hold on the
// buttons are released while the chord keeps playing. Re-voicing controls
// key off this, otherwise changing octave or spacing under Hold does
// nothing -- which is exactly when you would reach for them.
let soundingKey = null;
// The last chord the harp was built from. Kept after the button is released
// so the strumpad stays playable without needing Hold on -- pressing a chord
// primes the harp, and it stays primed until the next chord.
let lastHarpKey = null;
let chordNotes = [];
let strumNotes = [];
let lastStrumSeg = -1, strumming = false;

function currentKey(){
  return heldRows.size ? [...heldRows].sort().join('') : soundingKey;
}

function specForKey(key){
  // Barry Harris rewrites the standard triads; in the alternate layout those
  // combinations are different chords entirely, so it does not apply there.
  if (altLayout){
    const a = ALT_CHORDS[key];
    return a ? { tones: a.tones, suffix: a.suffix } : null;
  }
  if (septOn){
    const t = SEPT[key];
    return t ? { tones: t.tones, suffix: ' ' + t.name + ' \u00b7 ' + t.ratio } : null;
  }
  const c = CHORDS[key];
  if (!c) return null;
  const useBarry = barryOn && c.barry;
  return { tones: useBarry ? c.barry : c.tones,
           suffix: useBarry ? c.bSuffix : c.suffix };
}

function chordSpec(){ return specForKey(currentKey()); }

// Inversion decides which chord tone sits at the bottom; spacing decides how
// far apart the voices sit. Drop voicings take the close position and drop
// the Nth voice counted from the TOP by an octave -- drop 2 the second from
// the top, drop 3 the third, drop 2+4 both. Spread moves the outer voices
// apart instead, which is wider but leaves the middle clustered.
function voiceChord(tones, base){
  let notes = tones.map(t => base + t).sort((a, b) => a - b);

  for (let i = 0; i < inversion; i++){
    notes[0] += 12;                 // lowest voice up an octave
    notes.sort((a, b) => a - b);
  }

  const n = notes.length;
  const DROPS = { 1: [2], 2: [3], 3: [2, 4] };
  if (spacing >= 1 && spacing <= 3){
    for (const d of DROPS[spacing]){
      const i = n - d;              // dth voice counted from the top
      if (i >= 0) notes[i] -= 12;   // a triad has no fourth voice to drop
    }
  } else if (spacing === 4){
    notes[0] -= 12;
    notes[n - 1] += 12;
  }
  notes.sort((a, b) => a - b);

  // Shift the whole voicing into the firmware's note table rather than
  // clamping individual notes, which would collapse voices onto each other.
  while (notes[notes.length - 1] > 96) notes = notes.map(x => x - 12);
  while (notes[0] < 24) notes = notes.map(x => x + 12);
  return notes;
}

function chordFor(){
  const spec = chordSpec();
  if (!spec) return [];
  return voiceChord(spec.tones, rootMidi(activeRoot) + chordOct * 12);
}

// The harp: chord tones stacked upward until twelve sections are filled, so
// a strum walks the chord rather than a scale.
function ladderFor(){
  const sc = harpScaleFor();
  if (!sc) return [];
  const n = strumCount();
  // Fold the tones into one octave and sort them. A chord can reach past an
  // octave -- the alternate layout's ninths hold a 14 -- and stacking those
  // by the octave would put the ninth above the next repeat's root, so the
  // strings stopped ascending. The harp plays the chord's pitch classes
  // across octaves, which is what a harp does anyway.
  const tones = [...new Set(sc.tones.map(t => ((t % 12) + 12) % 12))].sort((a, b) => a - b);

  // Start an octave below the chord so there is room to climb, aligned to the
  // scale's own root rather than the chord's.
  const anchor = rootMidi(activeRoot) - 12 + strumOct * 12;
  let base = Math.floor(anchor / 12) * 12 + sc.root;
  if (base > anchor) base -= 12;

  let out = [];
  for (let i = 0; i < n; i++){
    out.push(base + tones[i % tones.length] + 12 * Math.floor(i / tones.length));
  }
  // A very short custom scale would otherwise climb an octave per string and
  // run off the top of the note table, so the octave is capped and the upper
  // strings repeat instead.
  while (Math.max.apply(null, out) > 96) out = out.map(x => x - 12);
  while (Math.min.apply(null, out) < 24) out = out.map(x => x + 12);
  out = out.map(x => Math.max(24, Math.min(96, x)));
  return out;
}

function releaseChord(){
  chordNotes.forEach(n => stopNote(n, 0));
  chordNotes = [];
}

// A chord change happens on a PRESS, never on a release. That is the
// minichord's rule and it matters: timing a release across three buttons is
// hopeless, and without it every complex chord would collapse through
// unwanted intermediate chords on the way out.
function pressRow(rootIdx, rowIdx){
  if (rootIdx !== activeRoot){ heldRows.clear(); activeRoot = rootIdx; }
  heldRows.add(rowIdx);
  soundingKey = [...heldRows].sort().join('');
  lastHarpKey = soundingKey;
  refreshChord();
}

function releaseRow(rowIdx){
  heldRows.delete(rowIdx);
  if (heldRows.size === 0 && !latchOn){
    releaseChord();
    soundingKey = null;
    updateStrum();                 // stays primed from lastHarpKey
  }
  paintChords();
}

// Re-form whatever is currently sounding. Chord notes cannot glide to a new
// voicing, so this restarts them; that retrigger IS the update.
function revoice(){
  if (currentKey()) refreshChord();
}

// Cents from equal temperament for each pitch class of the chord the matrix
// is on, or off. By pitch class, so the harp's strings in every octave share
// the chord's tuning. Only sent once the switch has been unlocked, so nobody
// else pays a line of traffic per chord.
// Shows the septimal switch. Remembered per browser, so the password is needed
// once. The switch pulses until it is first used, since it appears in the
// chord matrix and the password box is elsewhere.
function unlockSeptimal(quiet){
  septUnlocked = true;
  try { localStorage.setItem('8b8.septimal', '1'); } catch(e){}
  const cell = document.getElementById('septCell');
  if (cell) cell.hidden = false;
  const sw = document.getElementById('septSw');
  if (sw && !quiet) sw.classList.add('fresh');
}

function septTable(){
  if (!septOn || altLayout) return 'off';
  const key = currentKey() || lastHarpKey;
  const t = key && SEPT[key];
  if (!t) return 'off';
  const pcs = new Array(12).fill(0);
  const r = rootPc(activeRoot);
  t.tones.forEach((tone, i) => { pcs[(r + tone) % 12] = t.cents[i]; });
  return pcs.join(',');
}
function sendSeptTable(){
  if (septUnlocked) send('PCT:' + septTable());
}

function refreshChord(){
  const spec = chordSpec();
  if (!spec) return;
  releaseChord();
  sendSeptTable();
  chordNotes = chordFor();
  chordNotes.forEach(n => playNote(n, 100, 0));
  updateStrum();
  const el = document.getElementById('chordName');
  if (el) el.textContent = rootName(activeRoot) + spec.suffix;
  paintChords();
}

// The buttons say what they will play, so switching layout relabels them
// rather than leaving the old names on a different set of chords.
function relabelChords(){
  document.querySelectorAll('.chordbtn').forEach(b => {
    const ri = b.dataset.root | 0, qi = b.dataset.q | 0;
    b.textContent = rootName(ri) + (altLayout ? ALT_ROW_SUFFIX[qi]
                                  : septOn ? SEPT_ROW_SHORT[qi] : QUALITY[qi].suffix);
  });
  // Barry rewrites the standard triads, so it has no effect in the alternate
  // layout or while the septimal set is on; the septimal switch has none in
  // the alternate layout.
  const sw = document.getElementById('barrySw');
  if (sw) sw.style.opacity = (altLayout || septOn) ? '0.35' : '';
  const ss = document.getElementById('septSw');
  if (ss) ss.style.opacity = altLayout ? '0.35' : '';
}

// What Rate, Depth and Motion actually do, per mode. Three controls cover
// eleven effects, so without this the panel names them for none of them.
const WARP_LABELS = [
  ['Rate', 'Depth', 'Motion'],                  // Off
  ['Retrigger', 'Interval', 'Drift'],           // Sync Buzz
  ['Chop rate', 'Gap', 'Drift'],                // Stutter
  ['Jump rate', 'Spread', 'Drift'],             // Scramble
  ['Zap rate', 'Sweep', 'Drift'],               // Zap
  ['Fall time', 'Distance', 'Drift'],           // Tape Stop
  ['Siren speed', 'Range', 'Drift'],            // Siren
  ['Crush rate', 'Bits', 'Drift'],              // Crush
  ['Ring freq', 'Amount', 'Drift'],             // Ring
  ['Crush rate', 'Bits', 'Drift'],              // Env Crush
  ['Buzz freq', 'Bite', 'Drift']                // SID Voice
];

// Parameter controls carry no id, so the three are found once by their
// starting labels inside the Warp Zone module and kept. The label is a text
// node followed by the CC tag, so only the text node is rewritten: replacing
// the whole label would drop the CC binding readout with it.
let warpNameEls = null;
let warpModeRow = null;

function findWarpControls(){
  const mods = [...document.querySelectorAll('.module')];
  const warp = mods.find(m => {
    const h = m.querySelector('h2');
    return h && h.textContent.trim() === 'Warp Zone';
  });
  if (!warp) return;
  const want = { Rate: 0, Depth: 1, Motion: 2 };
  warpNameEls = [null, null, null];
  warp.querySelectorAll('.ctl .name').forEach(n => {
    const txt = (n.childNodes[0] && n.childNodes[0].nodeValue || '').trim();
    if (txt in want) warpNameEls[want[txt]] = n;
    // An enum renders as a row of buttons, not a select, so the mode is read
    // from which button is active rather than from a value.
    if (txt === 'Mode') warpModeRow = n.closest('.ctl').querySelector('.enum-row');
  });
}

function paintWarpLabels(){
  if (!warpNameEls) findWarpControls();
  if (!warpNameEls || !warpModeRow) return;
  const btns = [...warpModeRow.querySelectorAll('.enum-btn')];
  const mode = Math.max(0, btns.findIndex(b => b.classList.contains('active')));
  const names = WARP_LABELS[mode % WARP_LABELS.length];
  warpNameEls.forEach((n, i) => {
    if (n && n.childNodes[0]) n.childNodes[0].nodeValue = names[i];
  });
}

function paintChords(){
  document.querySelectorAll('.chordbtn').forEach(b => {
    const key = currentKey() || '';
    const on = (b.dataset.root | 0) === activeRoot && key.indexOf(String(b.dataset.q)) >= 0;
    b.classList.toggle('latched', on && latchOn);
    b.classList.toggle('down', on && !latchOn);
  });
}

// Vertical runs high at the top, like a harp stood on end; horizontal runs
// low at the left, like a keyboard. Rebuilt on a change rather than reversed
// with CSS, so the segment order always matches what is under the finger.
// Every string says what it plays. Rebuilt whenever the ladder changes, so
// the labels follow the chord, the harp mode and the octave.
function labelStrum(){
  document.querySelectorAll('.strum .seg').forEach(el => {
    const i = el.dataset.seg | 0;
    const span = el.firstChild;
    if (!span) return;
    span.textContent = (i < strumNotes.length) ? noteName(strumNotes[i]) : '';
  });
}

// One place to rebuild the ladder, so the labels can never drift from it.
function updateStrum(){
  strumNotes = ladderFor();
  labelStrum();
}

function buildStrumSegments(){
  const strum = document.getElementById('strum');
  if (!strum) return;
  const n = strumCount();
  strum.innerHTML = '';
  strum.classList.toggle('horiz', strumLayout === 'h');
  strum.classList.toggle('grid', strumLayout === 'grid');
  if (strumLayout === 'v'){
    const lbl = document.createElement('div');
    lbl.className = 'label'; lbl.textContent = 'STRUM';
    strum.appendChild(lbl);
  }

  // Vertical runs high at the top like a harp stood on end. Horizontal runs
  // low at the left like a keyboard. The grid fills bottom-left upward, so a
  // sweep left to right rises and then carries on in the row above.
  const order = [];
  if (strumLayout === 'v'){
    for (let i = n - 1; i >= 0; i--) order.push(i);
  } else if (strumLayout === 'h'){
    for (let i = 0; i < n; i++) order.push(i);
  } else {
    const rows = Math.ceil(n / 3);
    for (let r = rows - 1; r >= 0; r--)
      for (let c = 0; c < 3; c++){
        const i = r * 3 + c;
        if (i < n) order.push(i);
      }
  }
  order.forEach(i => {
    const seg = document.createElement('div');
    seg.className = 'seg'; seg.dataset.seg = i;
    seg.appendChild(document.createElement('span'));
    strum.appendChild(seg);
  });
  labelStrum();
}
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
